qvarker/Cyclone-PCB-Factory/Hardware/CYCLONE_2/SampleGcodes/DTMF-Decoder/KicadFiles/Layout.png

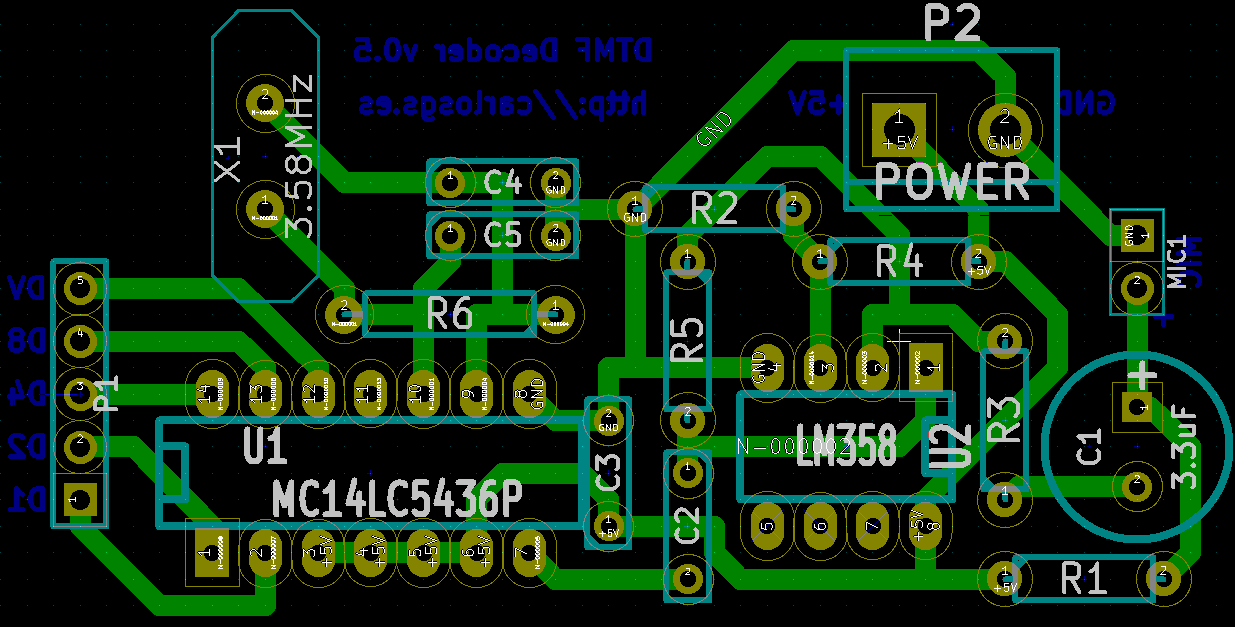
Hardware/CYCLONE_2/SampleGcodes/DTMF-Decoder/KicadFiles/Layout.png
