qvarker/Cyclone-PCB-Factory/Hardware/CYCLONE_2/SampleGcodes/DTMF-Decoder/KicadFiles/Schematic.png

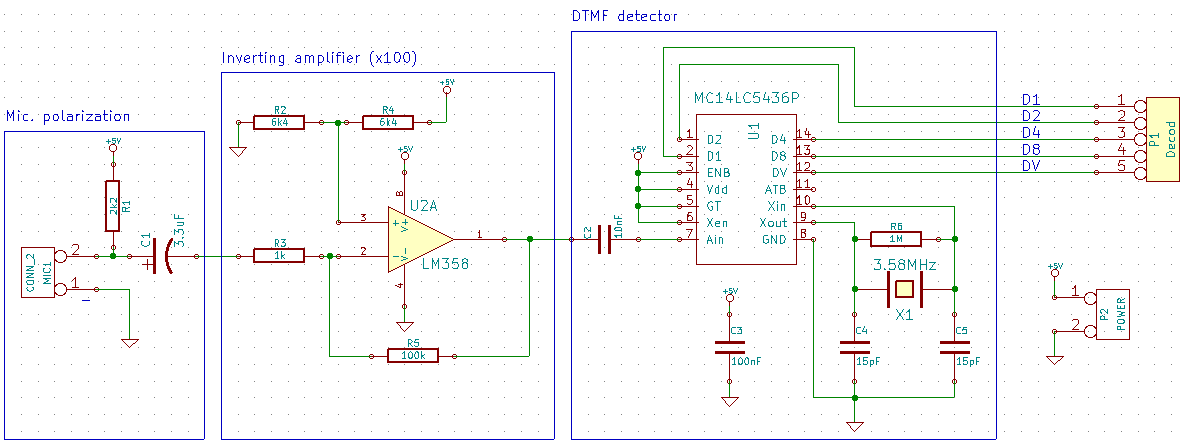
Hardware/CYCLONE_2/SampleGcodes/DTMF-Decoder/KicadFiles/Schematic.png
