qvarker/Cyclone-PCB-Factory/Hardware/CYCLONE_2/SampleGcodes/DTMF-Decoder/rapid-pcb-parameters/6.png

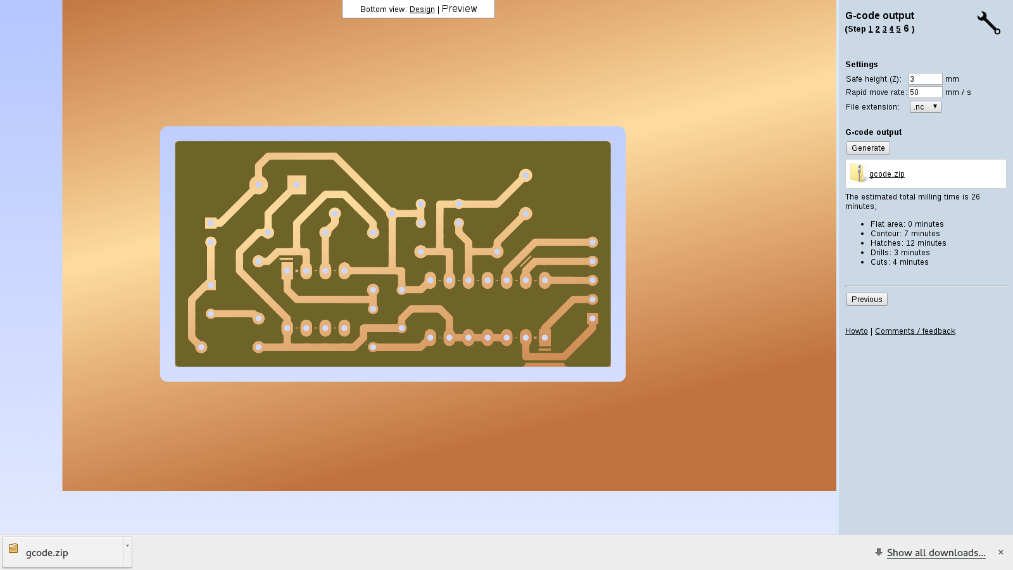
Hardware/CYCLONE_2/SampleGcodes/DTMF-Decoder/rapid-pcb-parameters/6.png
