qvarker/Cyclone-PCB-Factory/Hardware/Spindle_Pen/img/IMG_2634_display_large.jpg

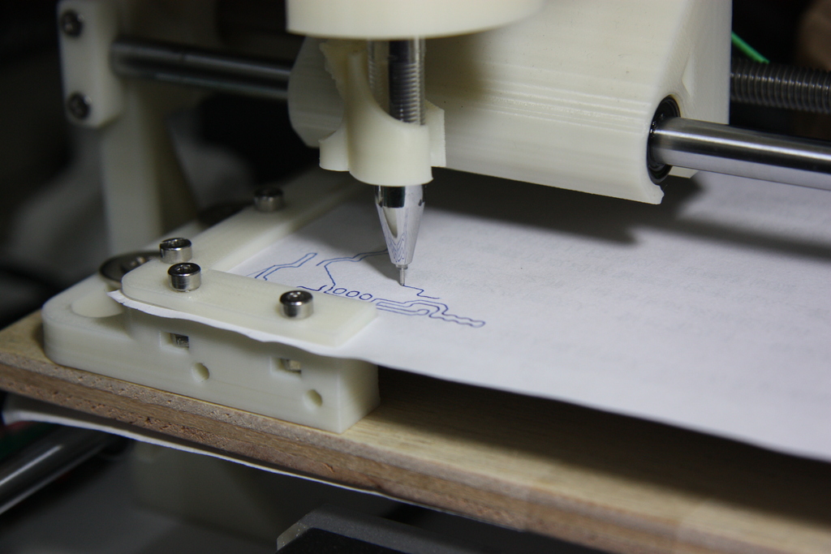
Hardware/Spindle_Pen/img/IMG_2634_display_large.jpg
