qvarker/Cyclone-PCB-Factory/Hardware/Spindle_Pen/img/IMG_9992_display_large.jpg

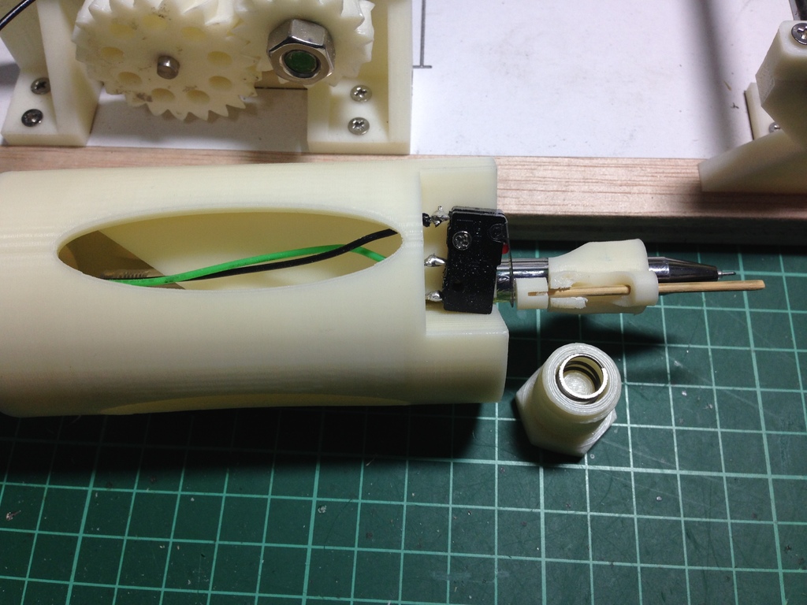
Hardware/Spindle_Pen/img/IMG_9992_display_large.jpg
