qvarker/Cyclone-PCB-Factory/Hardware/Spindle_Pen/img/SpindlePen_display_large.jpg

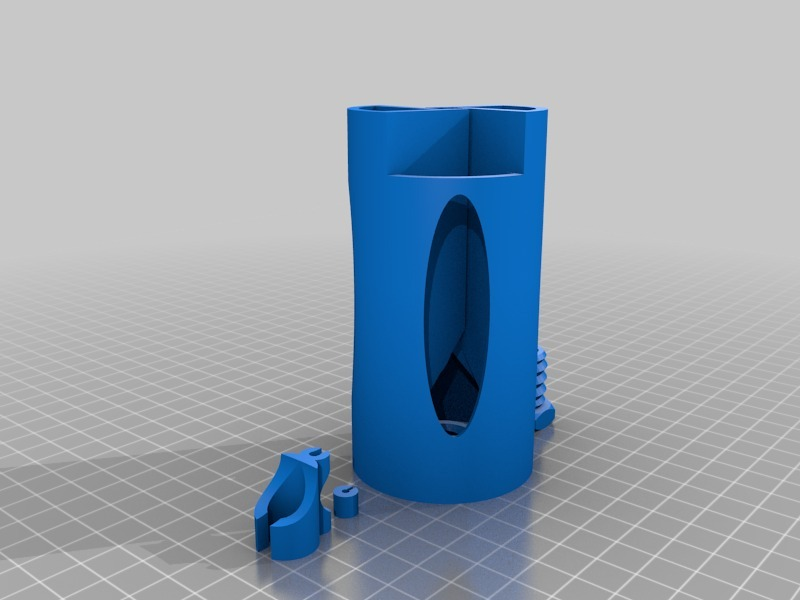
Hardware/Spindle_Pen/img/SpindlePen_display_large.jpg
