qvarker/Cyclone-PCB-Factory/Hardware/yOPERO/CNC_shieldBox/AnimationSource/frame00000.png

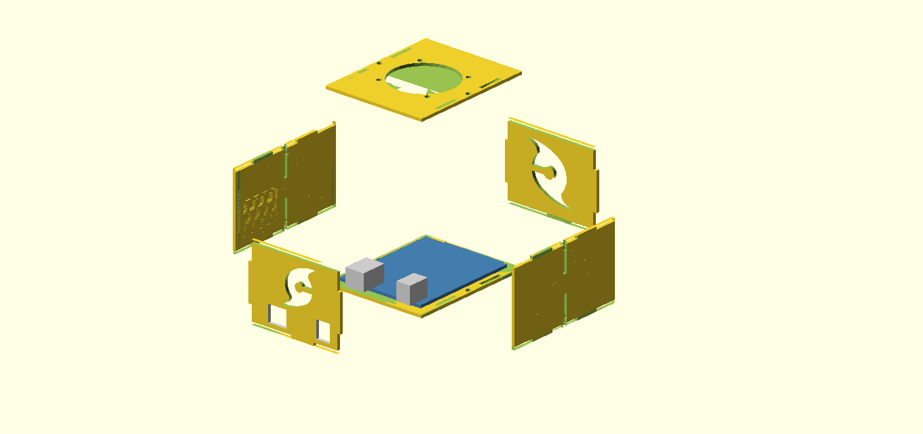
Hardware/yOPERO/CNC_shieldBox/AnimationSource/frame00000.png
