qvarker/Cyclone-PCB-Factory/Hardware/yOPERO/CNC_shieldBox/AnimationSource/frame00001.png

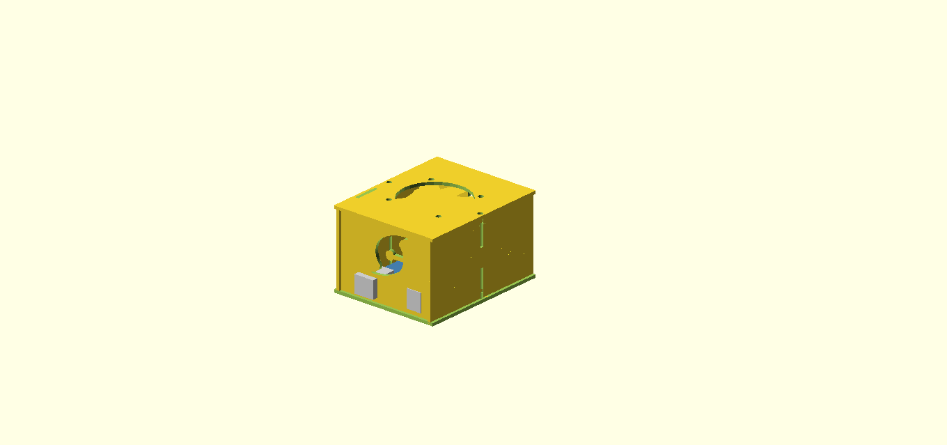
Hardware/yOPERO/CNC_shieldBox/AnimationSource/frame00001.png
