qvarker/Cyclone-PCB-Factory/Hardware/yOPERO/CNC_shieldBox/AnimationSource/frame00005.png

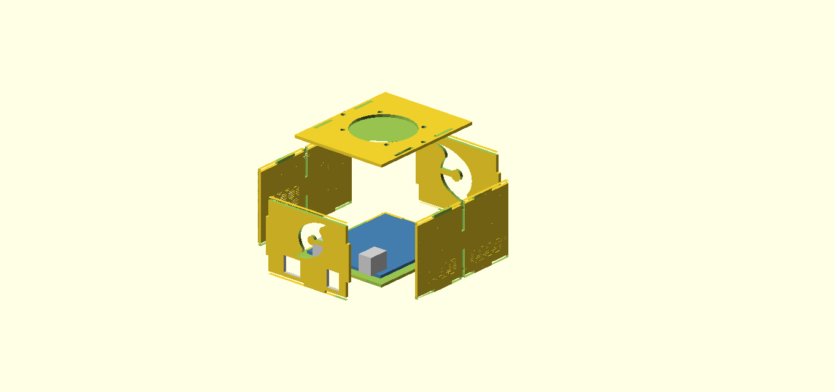
Hardware/yOPERO/CNC_shieldBox/AnimationSource/frame00005.png
