qvarker/Cyclone-PCB-Factory/Hardware/yOPERO/CNC_shieldBox/AnimationSource/frame00008.png

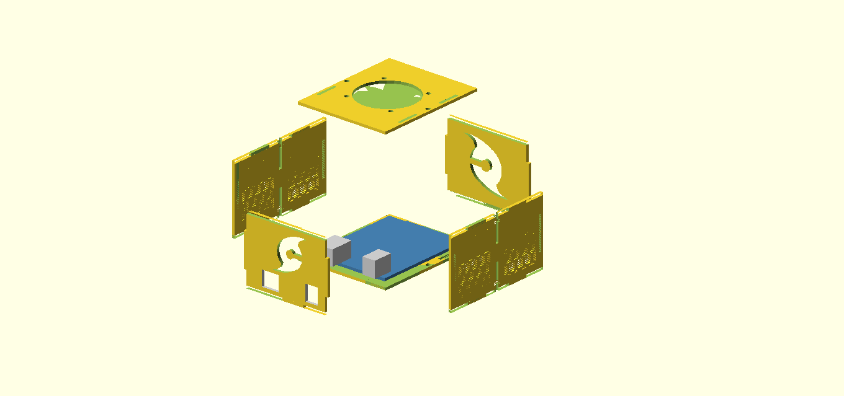
Hardware/yOPERO/CNC_shieldBox/AnimationSource/frame00008.png
