qvarker/Cyclone-PCB-Factory/Media/Cyclone_built_v0.9.5.jpg

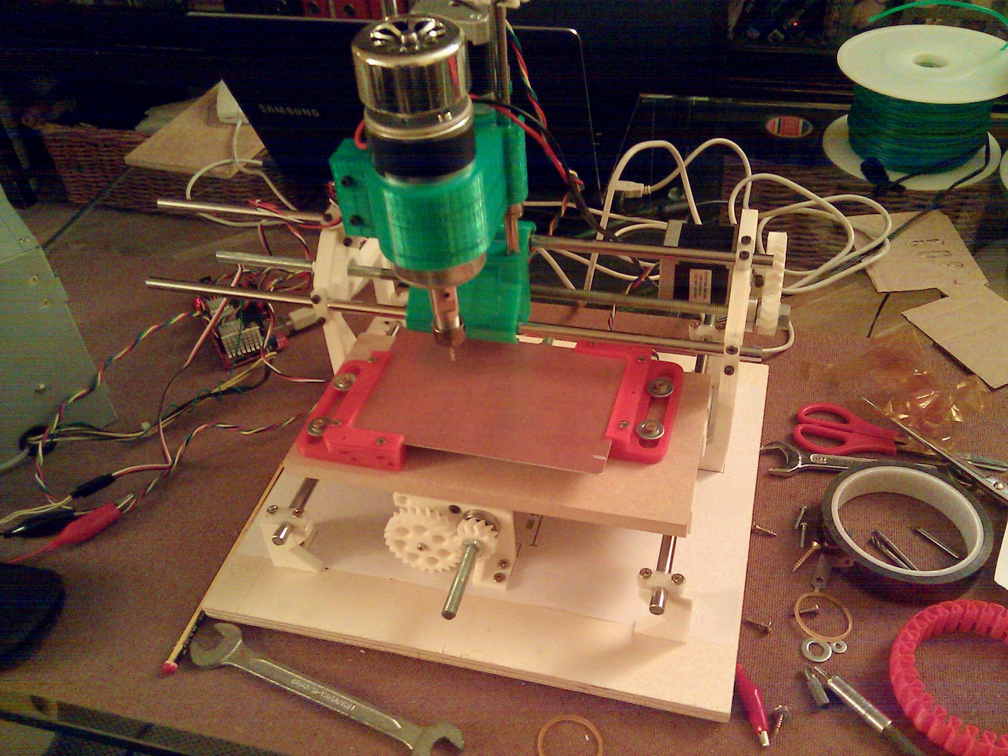
Media/Cyclone_built_v0.9.5.jpg
