qvarker/Cyclone-PCB-Factory/Media/Cyclone_render_v0.9.6.png

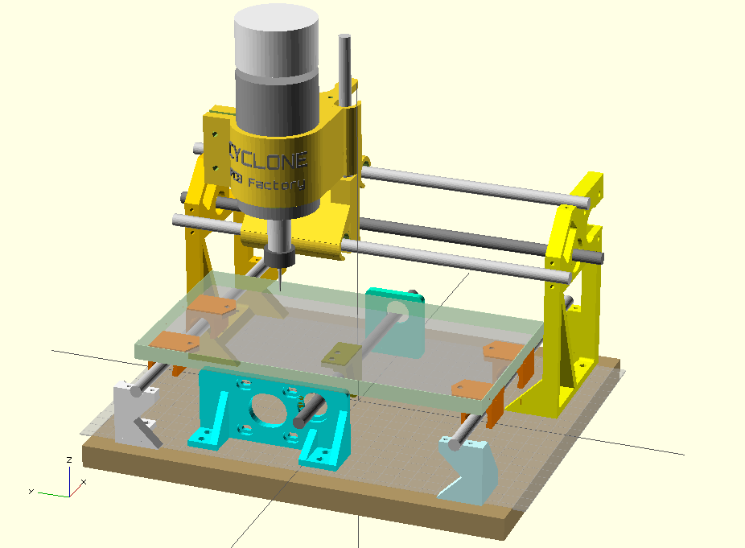
Media/Cyclone_render_v0.9.6.png
