qvarker/Cyclone-PCB-Factory/Media/Z_probing_interpolated.png

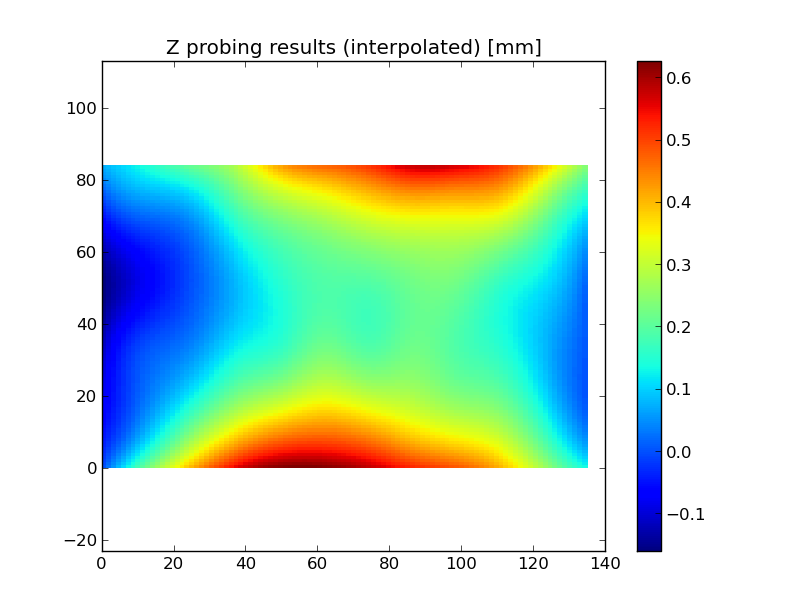
Media/Z_probing_interpolated.png
