qvarker/Cyclone-PCB-Factory/Media/Z_probing_raw.png

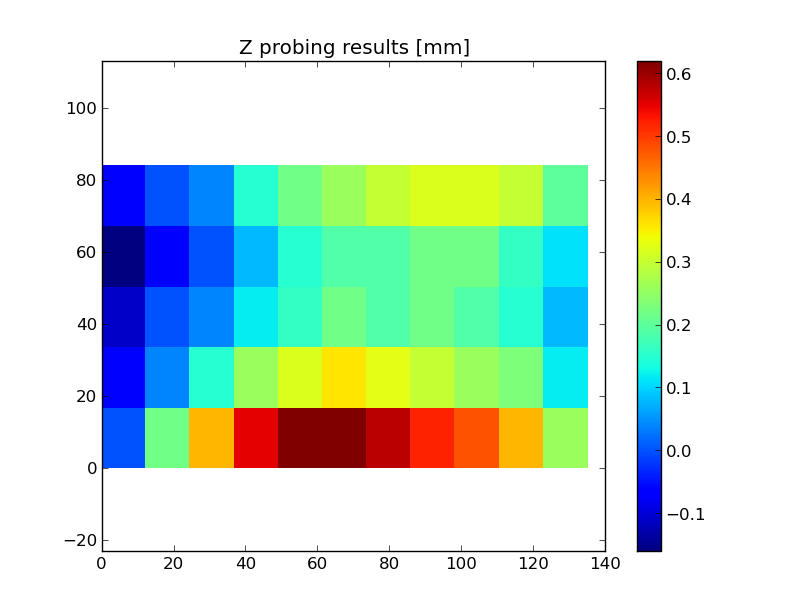
Media/Z_probing_raw.png
