qvarker/Cyclone-PCB-Factory/Software/PythonScripts/Images/DTMF.png

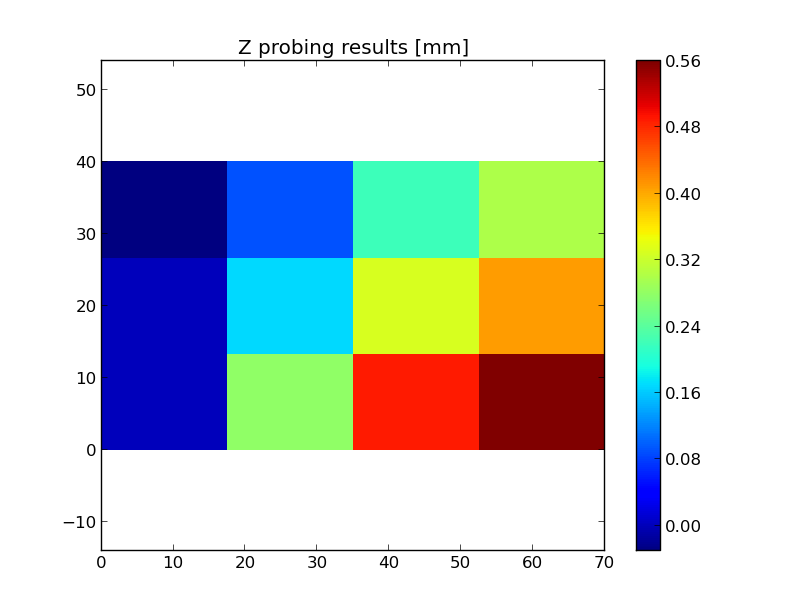
Software/PythonScripts/Images/DTMF.png
