qvarker/Cyclone-PCB-Factory/Software/PythonScripts/Images/GUI_v0.2.png

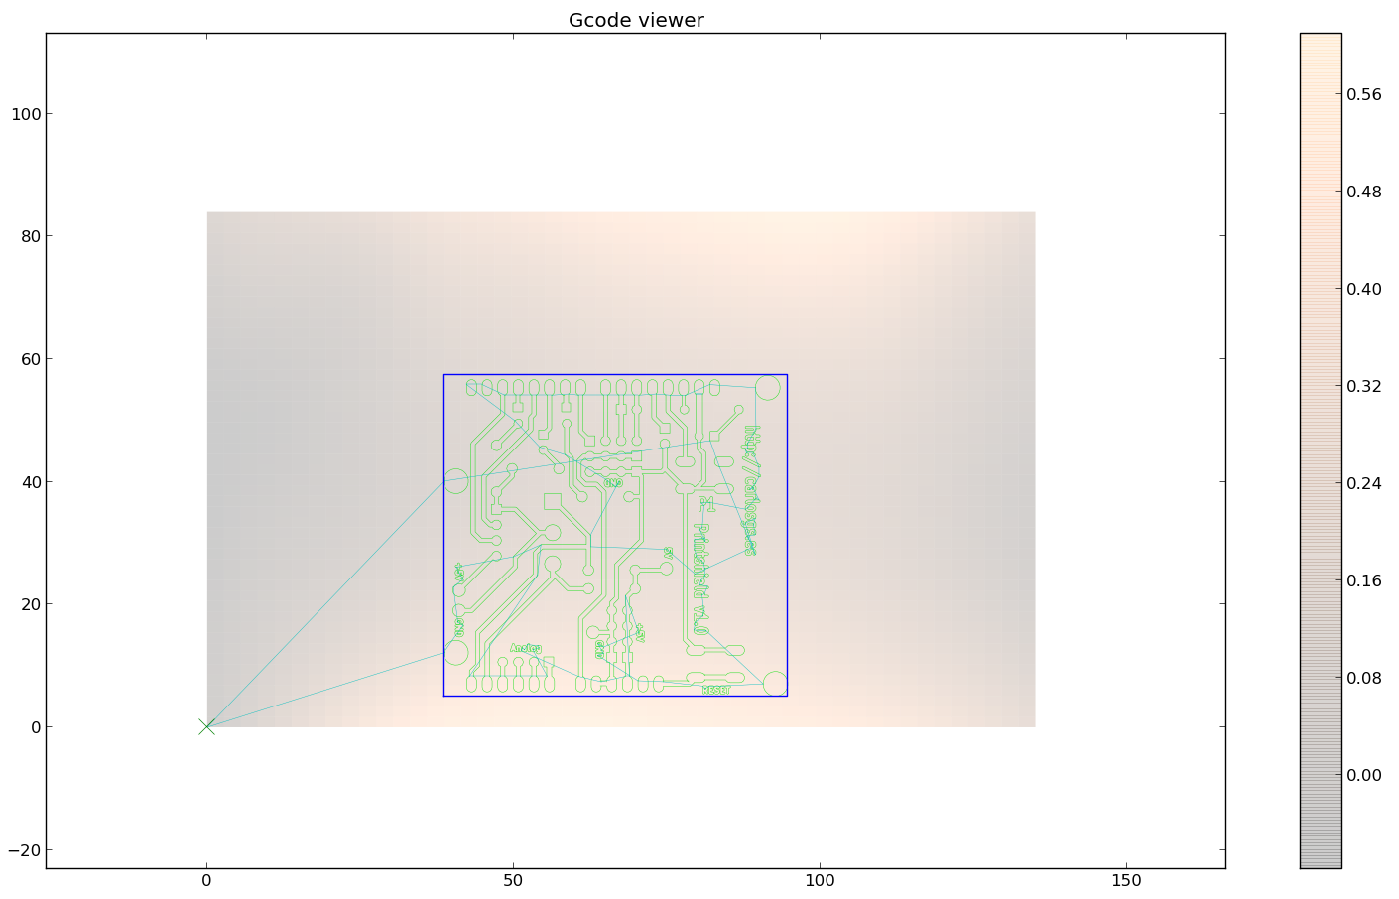
Software/PythonScripts/Images/GUI_v0.2.png
