qvarker/Cyclone-PCB-Factory/Software/PythonScripts/Images/viewGcode.png

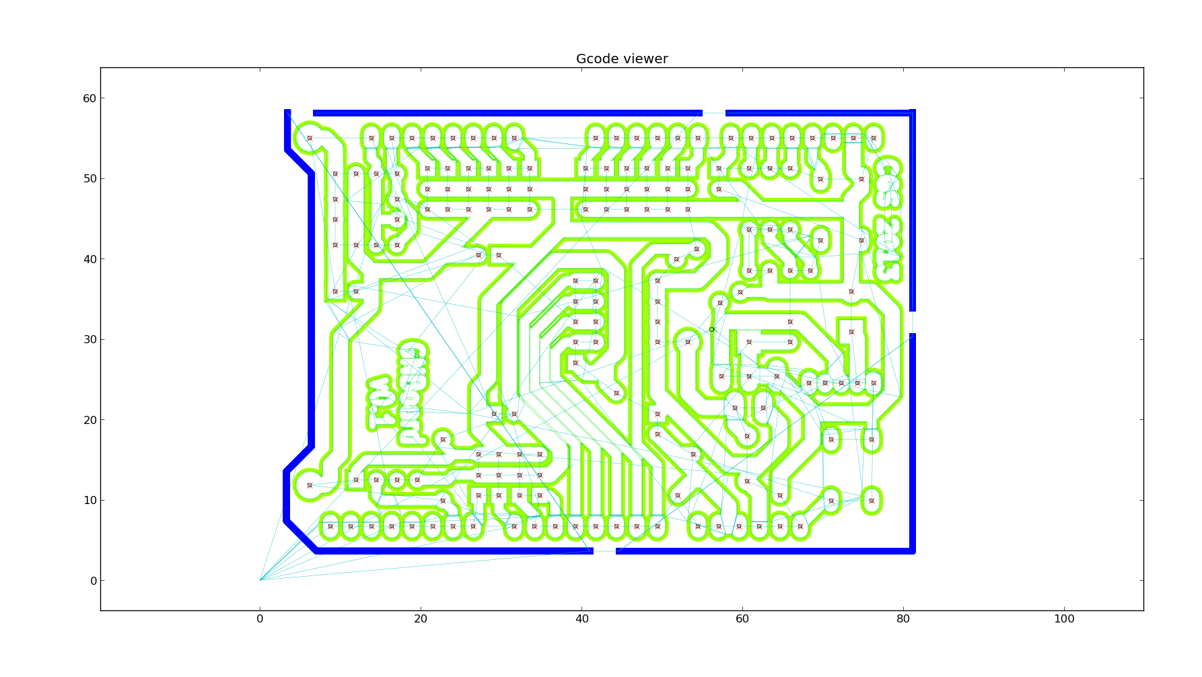
Software/PythonScripts/Images/viewGcode.png
