qvarker/Cyclone-PCB-Factory/Software/PythonScripts/Replath/replath/fullplot.bmp

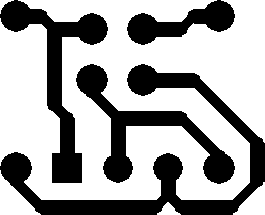
Software/PythonScripts/Replath/replath/fullplot.bmp
