qvarker/Cyclone-PCB-Factory/Hardware/smooth_rod_fix/stl/smooth_rod_fix.stl

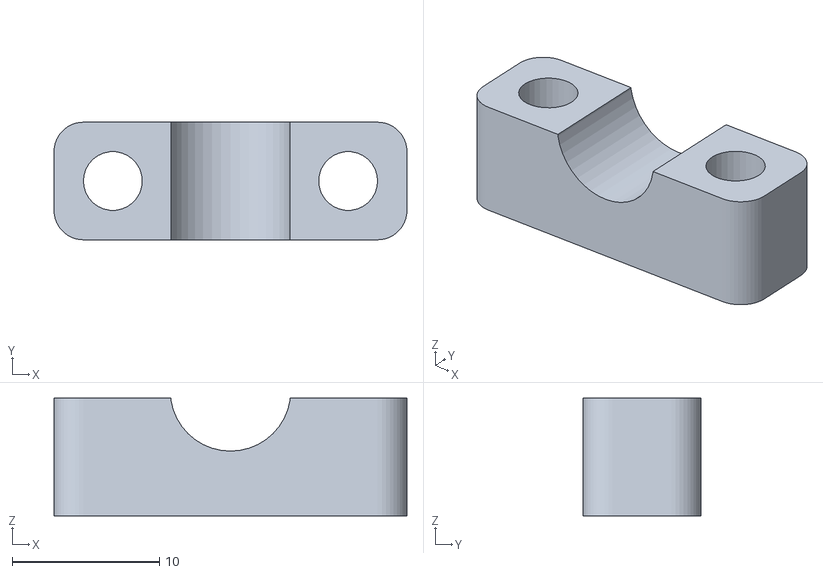
[picture p53: CAD file, 2014-09-08]
Hardware/smooth_rod_fix/stl/smooth_rod_fix.stl
24.0 x 8.00 x 8.00
