qvarker/Cyclone-PCB-Factory/Hardware/Vacuum_cleaner_attachment/prev/corrugated/vacuum_cleaner_attachment.stl

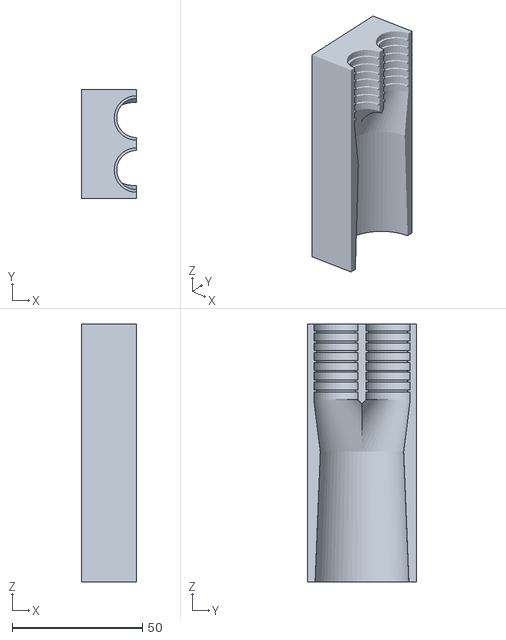
[picture p54: CAD file, 2014-09-08]
Hardware/Vacuum_cleaner_attachment/prev/corrugated/vacuum_cleaner_attachment.stl
21.0 x 42.0 x 99.0
