qvarker/Cyclone-PCB-Factory/Hardware/Vacuum_cleaner_attachment/prev/vacuum_cleaner_attachment_2_3.stl

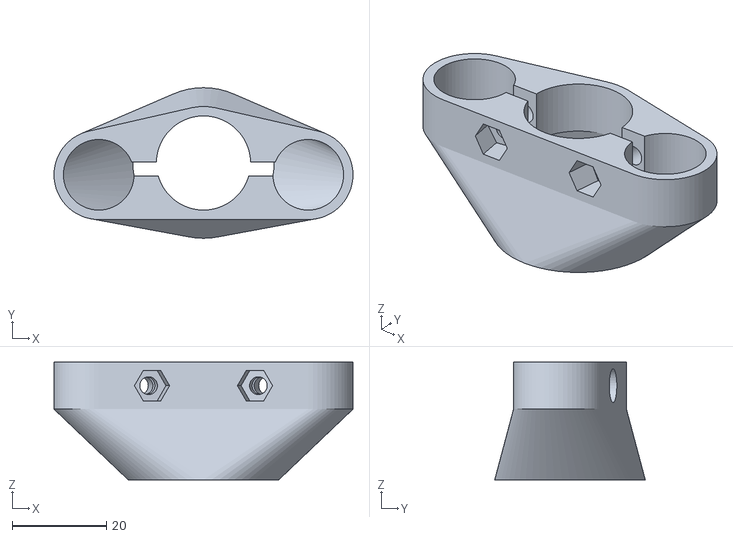
[picture p55: CAD file, 2014-09-08]
Hardware/Vacuum_cleaner_attachment/prev/vacuum_cleaner_attachment_2_3.stl
63.5 x 32.0 x 25.0
