qvarker/Cyclone-PCB-Factory/Hardware/Vacuum_cleaner_attachment/vacuum_cleaner_attachment.stl

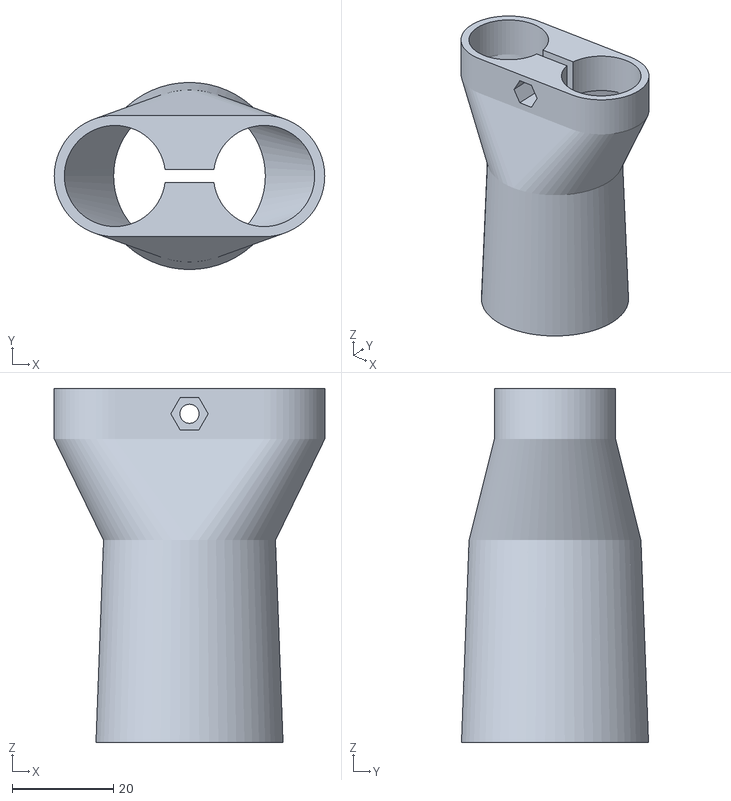
[picture p56: CAD file, 2014-09-08]
Hardware/Vacuum_cleaner_attachment/vacuum_cleaner_attachment.stl
53.5 x 37.0 x 70.0
