qvarker/Cyclone-PCB-Factory/Hardware/XZ_axis/stl/gears/motor_gear.stl

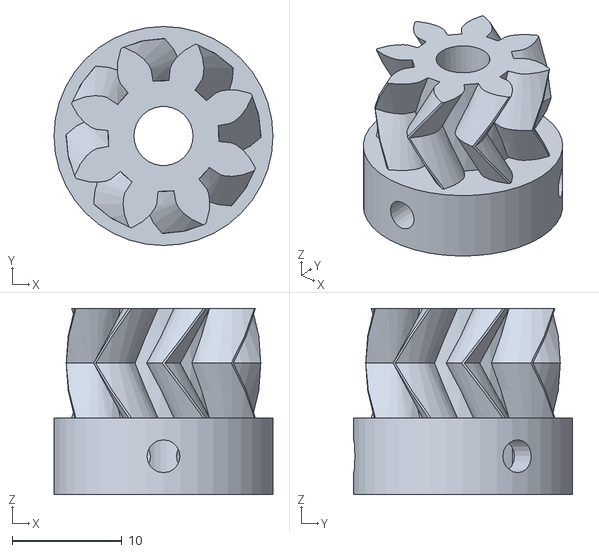
[picture p57: CAD file, 2014-09-08]
Hardware/XZ_axis/stl/gears/motor_gear.stl
20.0 x 20.0 x 17.0
