qvarker/Cyclone-PCB-Factory/Hardware/XZ_axis/stl/Z_carriage_bottom.stl

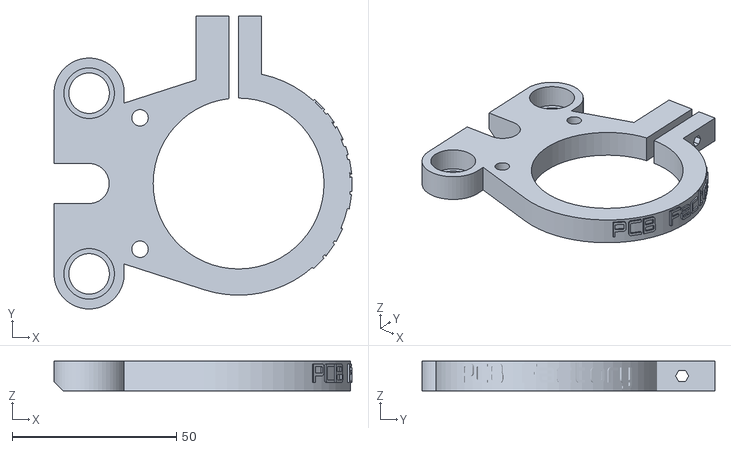
[picture p58: CAD file, 2014-09-08]
Hardware/XZ_axis/stl/Z_carriage_bottom.stl
90.7 x 89.2 x 9.00
