qvarker/Cyclone-PCB-Factory/Hardware/Y_axis/stl/motor_stand.stl

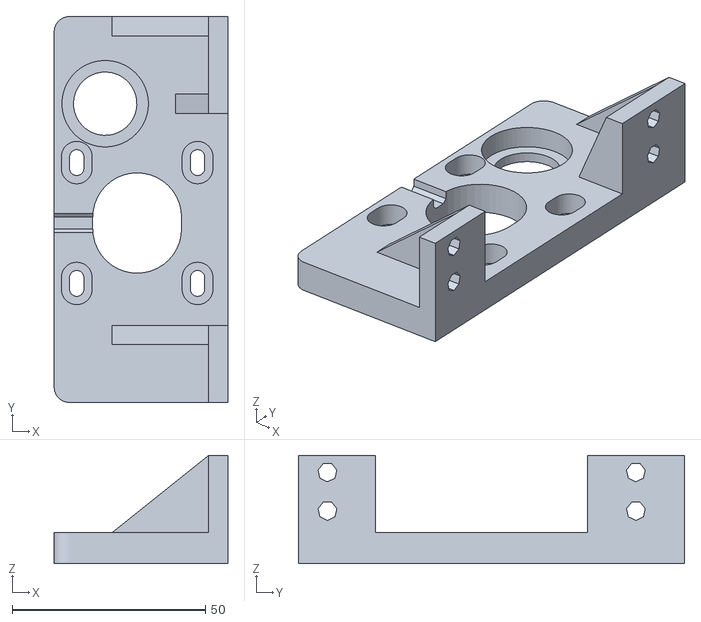
[picture p59: CAD file, 2014-09-08]
Hardware/Y_axis/stl/motor_stand.stl
45.0 x 100.0 x 28.0
