qvarker/Cyclone-PCB-Factory/Hardware/Y_axis/stl/Y_rod_idlers/Y_rod_idler_right.stl

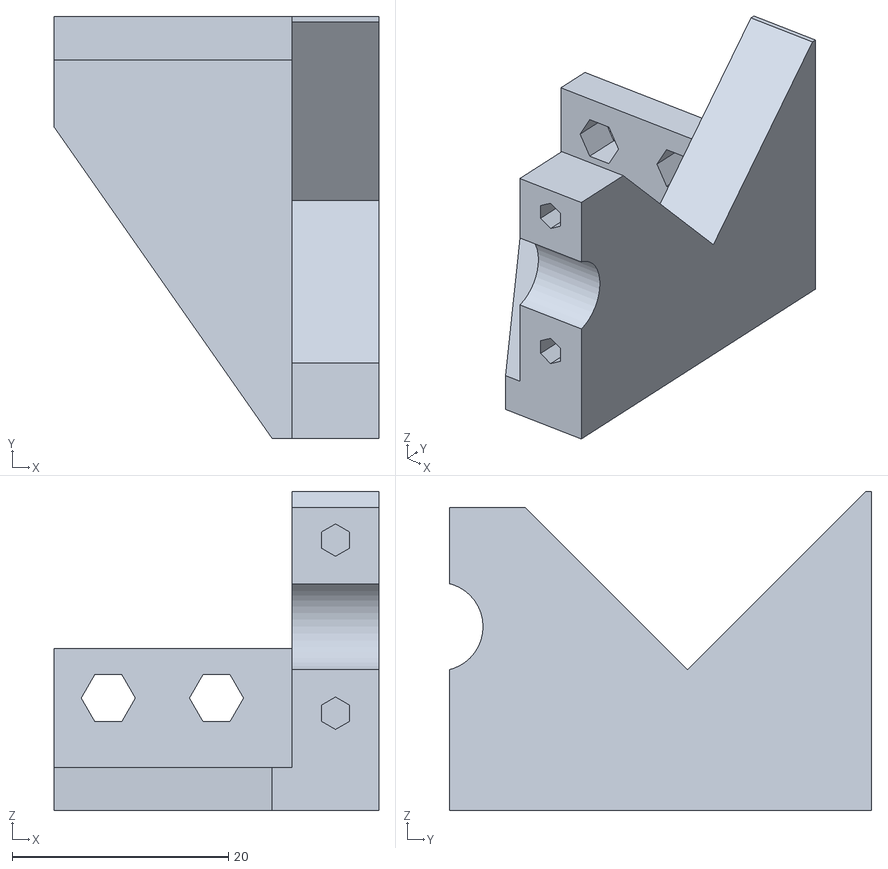
[picture p60: CAD file, 2014-09-08]
Hardware/Y_axis/stl/Y_rod_idlers/Y_rod_idler_right.stl
30.0 x 39.0 x 29.5
