qvarker/Cyclone-PCB-Factory/Hardware/yOPERO/CNC_shieldBox/STL/back.stl

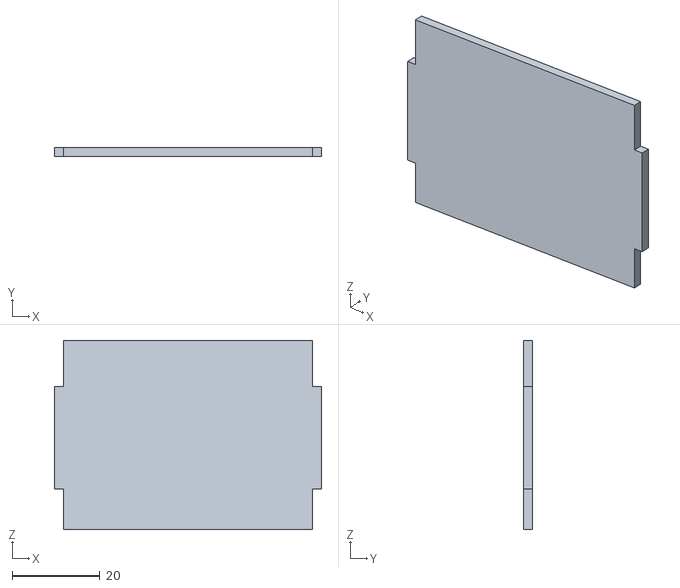
[picture p61: CAD file, 2014-09-08]
Hardware/yOPERO/CNC_shieldBox/STL/back.stl
60.7 x 2.00 x 43.0
