qvarker/Cyclone-PCB-Factory/Hardware/yOPERO/CNC_shieldBox/STL/Template/cncElectronicsShield.stl

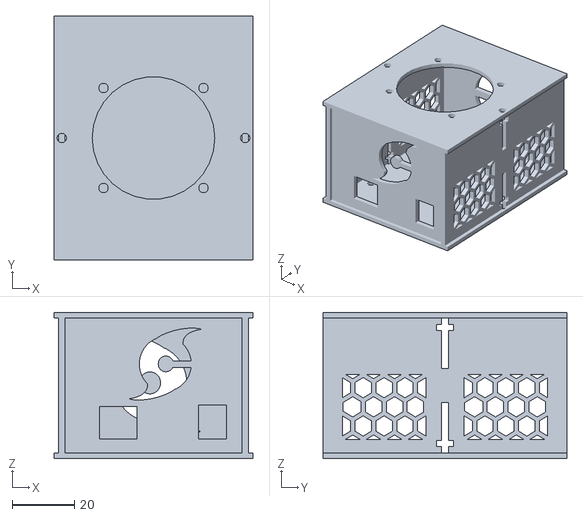
[picture p62: CAD file, 2014-09-08]
Hardware/yOPERO/CNC_shieldBox/STL/Template/cncElectronicsShield.stl
63.7 x 78.0 x 46.8
