qvarker/Cyclone-PCB-Factory/Hardware/yOPERO/Cyclone_Template/output/template_workbed.dxf

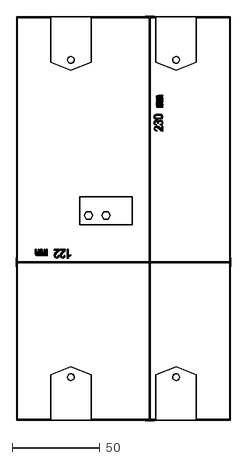
[picture p63: CAD file, 2014-09-08]
Hardware/yOPERO/Cyclone_Template/output/template_workbed.dxf
122.5 x 230.5
