qvarker/Cyclone-PCB-Factory/Hardware/yOPERO/Gears/stl/rod_gear.stl

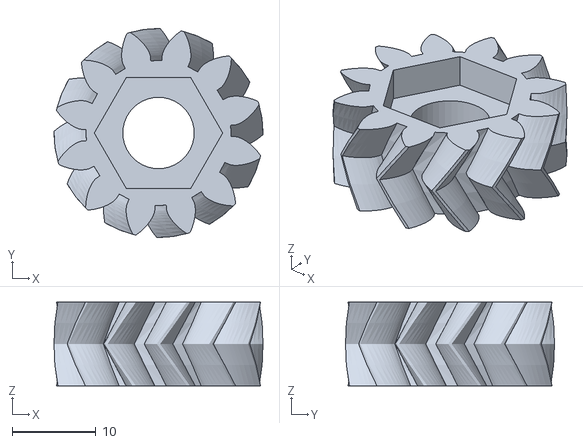
[picture p64: CAD file, 2014-09-08]
Hardware/yOPERO/Gears/stl/rod_gear.stl
24.9 x 24.9 x 10.0
