qvarker/Cyclone-PCB-Factory/Hardware/yOPERO/main_frame/stl/frame_hex_back support.stl

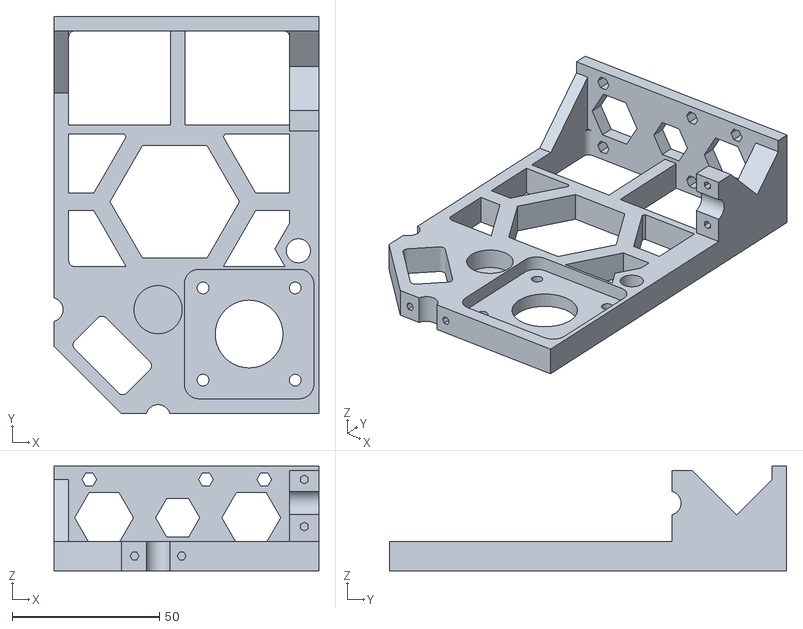
[picture p65: CAD file, 2014-09-08]
Hardware/yOPERO/main_frame/stl/frame_hex_back support.stl
90.0 x 135.0 x 35.5
