qvarker/Cyclone-PCB-Factory/Hardware/yOPERO/main_frame/stl/not used/frame.stl

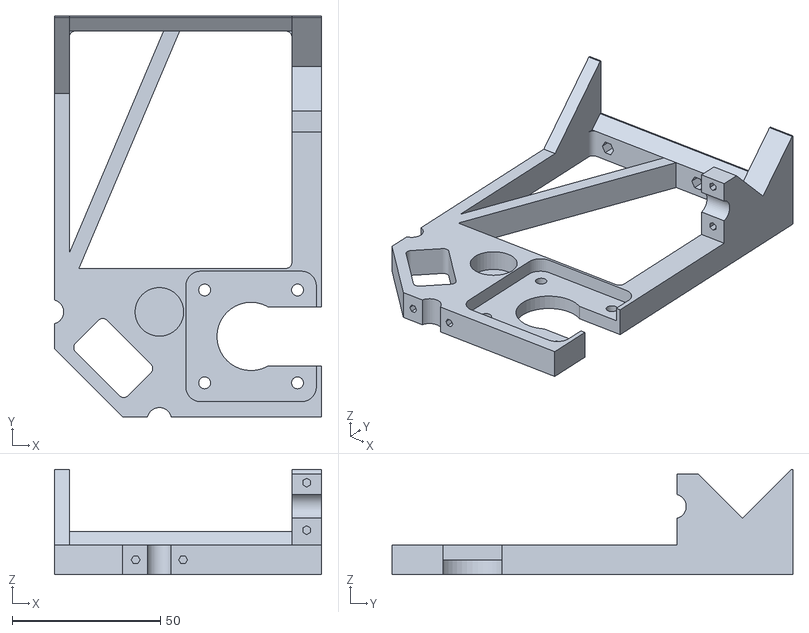
[picture p66: CAD file, 2014-09-08]
Hardware/yOPERO/main_frame/stl/not used/frame.stl
90.0 x 135.0 x 35.5
