qvarker/Cyclone-PCB-Factory/Hardware/yOPERO/smooth_rod_fix/stl/smooth_rod_fix_x8.stl

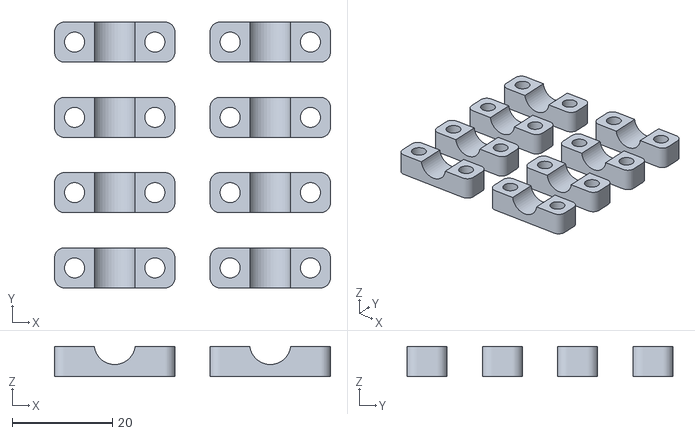
[picture p67: CAD file, 2014-09-08]
Hardware/yOPERO/smooth_rod_fix/stl/smooth_rod_fix_x8.stl
55.0 x 53.0 x 6.00
