qvarker/Cyclone-PCB-Factory/Hardware/yOPERO/XZ_axis/stl/X_carriage_YOP.stl

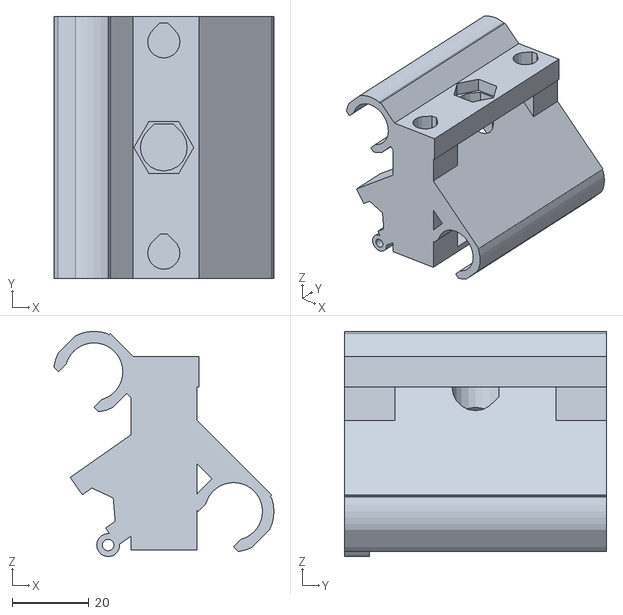
[picture p68: CAD file, 2014-09-08]
Hardware/yOPERO/XZ_axis/stl/X_carriage_YOP.stl
57.3 x 68.2 x 58.6
