qvarker/Cyclone-PCB-Factory/Hardware/yOPERO/Y_axis/cyclone_logo1.dxf

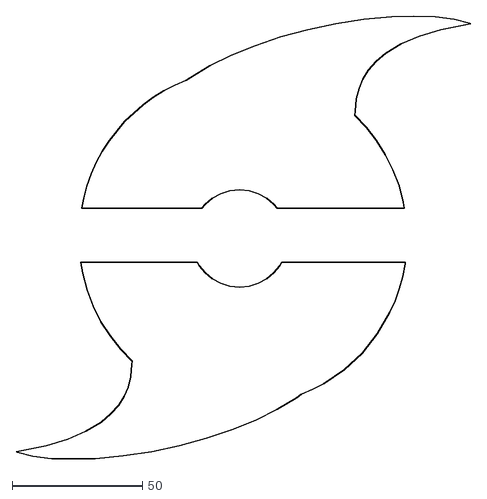
[picture p69: CAD file, 2014-09-08]
Hardware/yOPERO/Y_axis/cyclone_logo1.dxf
174.3 x 169.6
