qvarker/Cyclone-PCB-Factory/Hardware/yOPERO/Y_axis/stl/motor_holder.stl

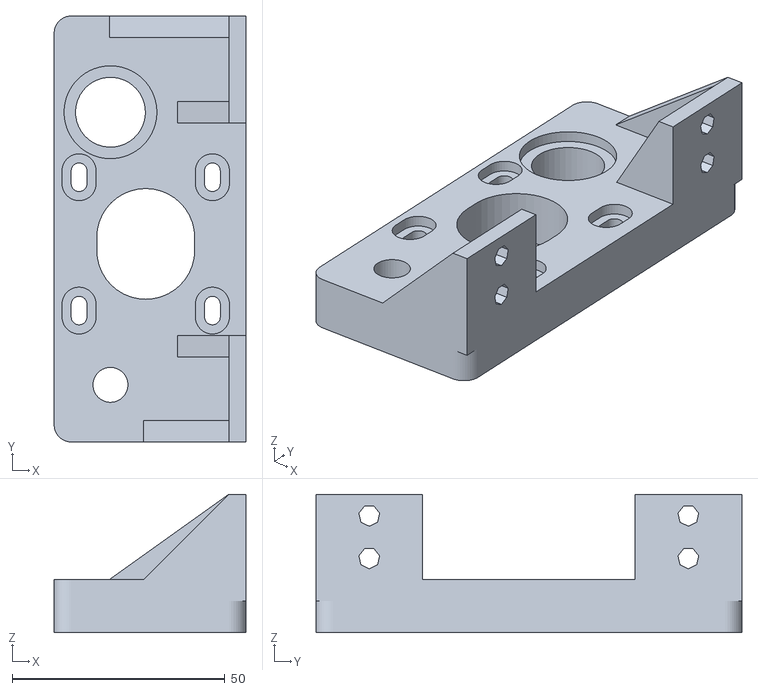
[picture p70: CAD file, 2014-09-08]
Hardware/yOPERO/Y_axis/stl/motor_holder.stl
45.0 x 100.0 x 32.5
