qvarker/Cyclone-PCB-Factory/Media/CycloneLogo_1/CycloneLogo_1.dxf

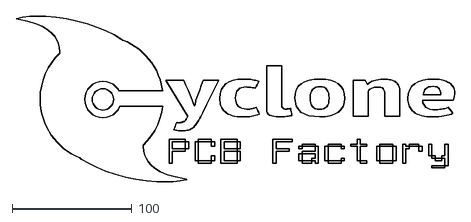
[picture p71: CAD file, 2014-09-08]
Media/CycloneLogo_1/CycloneLogo_1.dxf
366.4 x 138.5
