qvarker/Cyclone-PCB-Factory/Hardware/CYCLONE_2/dxf/oshw.dxf

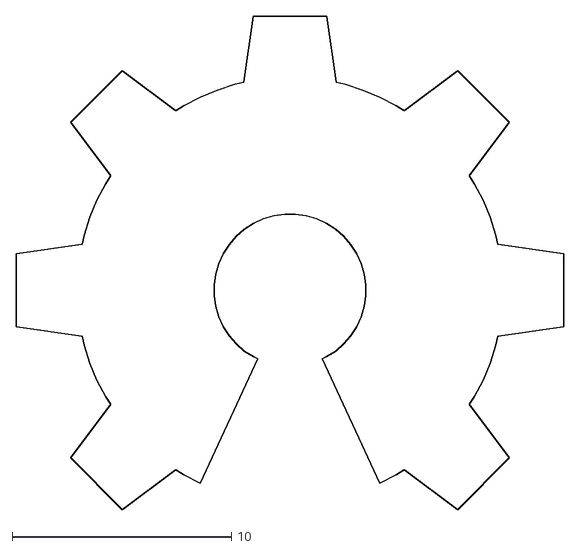
[picture p72: CAD file, 2014-08-22]
Hardware/CYCLONE_2/dxf/oshw.dxf
25.0 x 22.5
