qvarker/Cyclone-PCB-Factory/Hardware/CYCLONE_2/freecad/Cyclone_X_rightFrame.fcstd

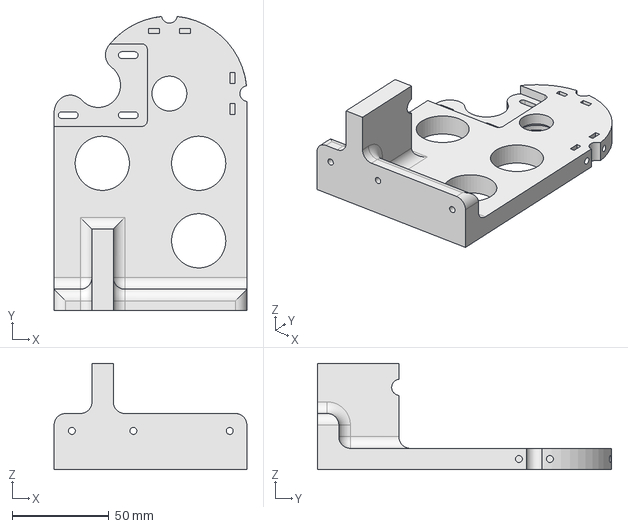
[picture p73: CAD file, 2014-09-10]
Hardware/CYCLONE_2/freecad/Cyclone_X_rightFrame.fcstd
99.5 x 151.8 x 54.9 mm
