qvarker/Cyclone-PCB-Factory/Hardware/CYCLONE_2/INHERITED/stl/vacuum_cleaner_attachment_2.stl

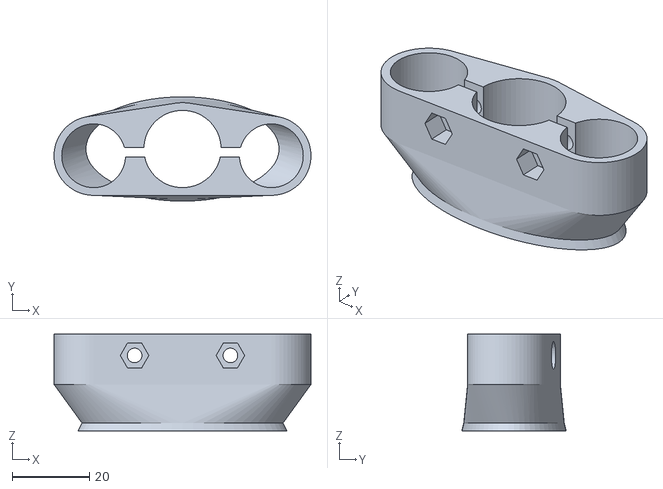
[picture p74: CAD file, 2014-09-08]
Hardware/CYCLONE_2/INHERITED/stl/vacuum_cleaner_attachment_2.stl
66.5 x 27.0 x 25.0
