qvarker/Cyclone-PCB-Factory/Hardware/CYCLONE_2/INHERITED/XYgears/XYmotor_gear.stl

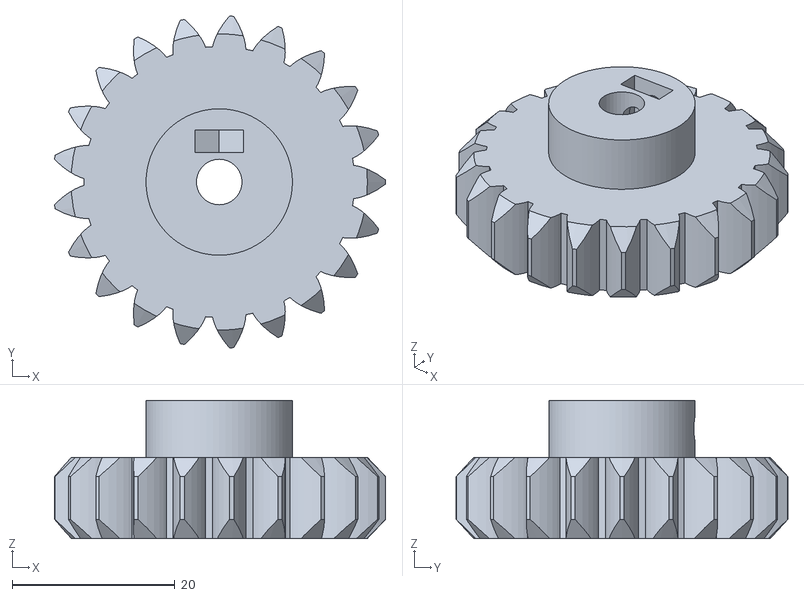
[picture p75: CAD file, 2014-08-22]
Hardware/CYCLONE_2/INHERITED/XYgears/XYmotor_gear.stl
40.7 x 40.8 x 17.0
