qvarker/Cyclone-PCB-Factory/Hardware/CYCLONE_2/INHERITED/Zgears/Zmotor_gear.stl

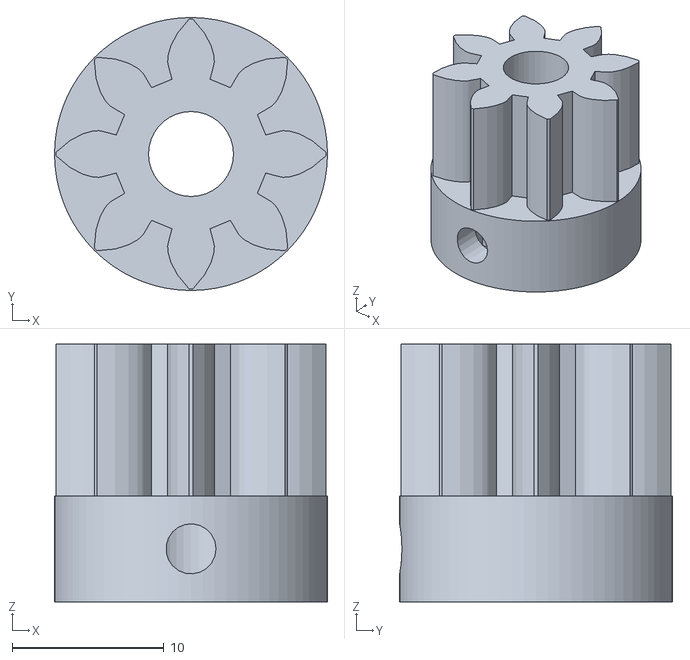
[picture p76: CAD file, 2014-08-22]
Hardware/CYCLONE_2/INHERITED/Zgears/Zmotor_gear.stl
18.0 x 18.0 x 17.0
