qvarker/Cyclone-PCB-Factory/Hardware/CYCLONE_2/output/ShorterVersion/Cyclone_XleftFrame.stl

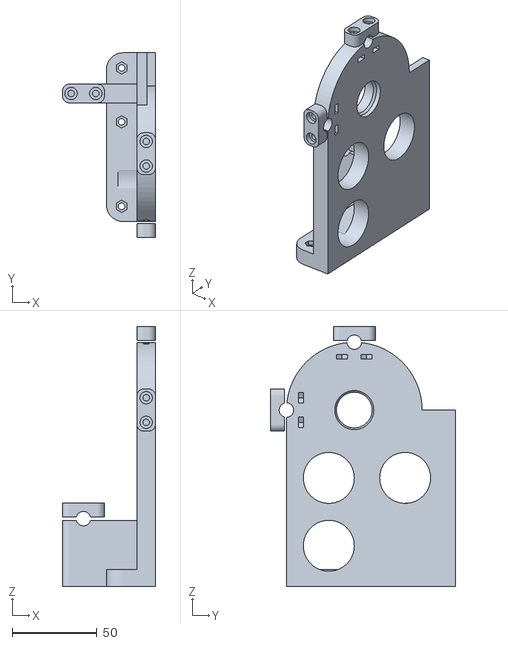
[picture p77: CAD file, 2014-09-08]
Hardware/CYCLONE_2/output/ShorterVersion/Cyclone_XleftFrame.stl
54.9 x 108.8 x 153.2
