qvarker/Cyclone-PCB-Factory/Hardware/CYCLONE_2/output/templates/Cyclone_workbed_template.dxf

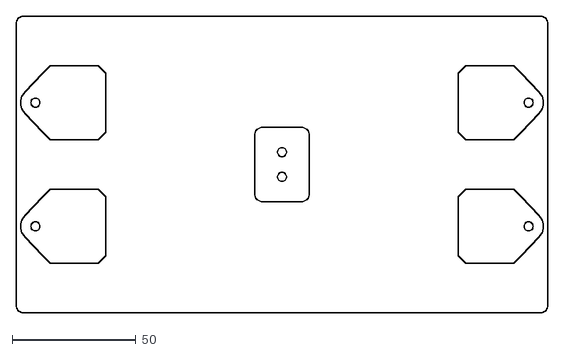
[picture p78: CAD file, 2014-08-22]
Hardware/CYCLONE_2/output/templates/Cyclone_workbed_template.dxf
215.0 x 120.0
