qvarker/Cyclone-PCB-Factory/Hardware/CYCLONE_2/output/templates/laserCut/Cyclone_workbed_8mm.dxf

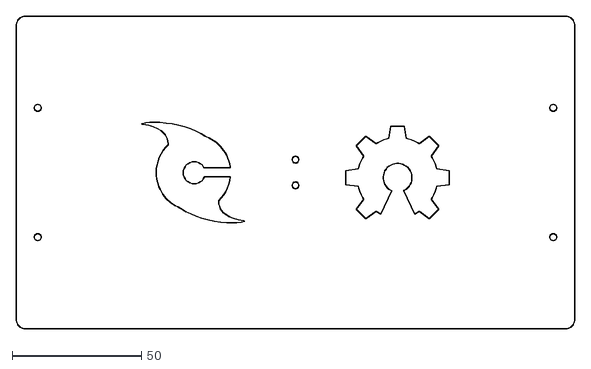
[picture p79: CAD file, 2014-08-22]
Hardware/CYCLONE_2/output/templates/laserCut/Cyclone_workbed_8mm.dxf
216.0 x 121.0
