qvarker/Cyclone-PCB-Factory/Hardware/CYCLONE_2/output/templates/laserCut/separate/Cyclone_base_drills.dxf

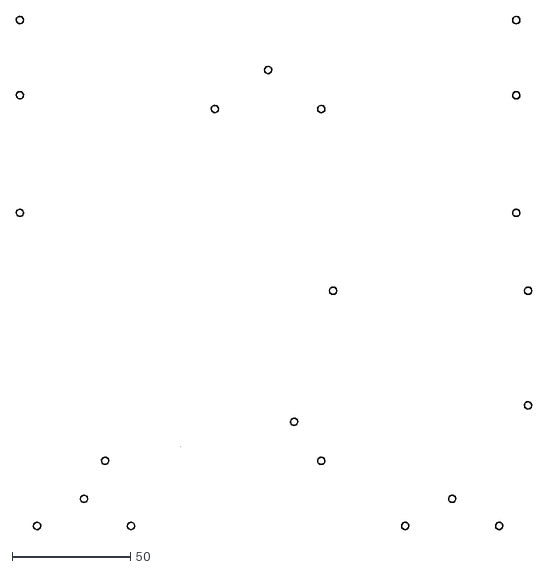
[picture p80: CAD file, 2014-08-22]
Hardware/CYCLONE_2/output/templates/laserCut/separate/Cyclone_base_drills.dxf
218.1 x 217.1
