qvarker/Cyclone-PCB-Factory/Hardware/Gears/stl/motor_gear_21.stl

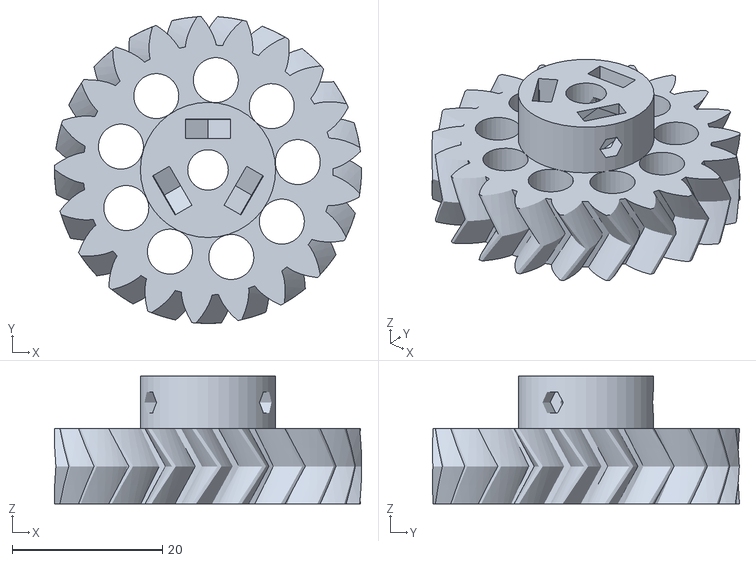
[picture p81: CAD file, 2014-09-08]
Hardware/Gears/stl/motor_gear_21.stl
40.9 x 40.9 x 17.0
