qvarker/Cyclone-PCB-Factory/Hardware/main_frame/Flat_DXFs/frame_nomotor.dxf

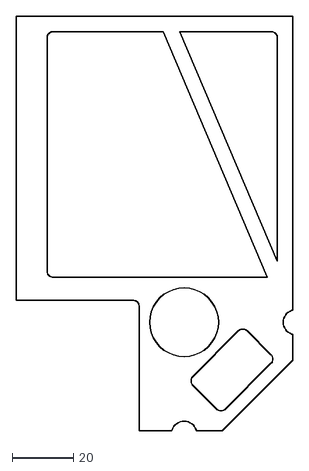
[picture p82: CAD file, 2014-09-08]
Hardware/main_frame/Flat_DXFs/frame_nomotor.dxf
90.0 x 135.0
