qvarker/Cyclone-PCB-Factory/Hardware/main_frame/stl/frame.stl

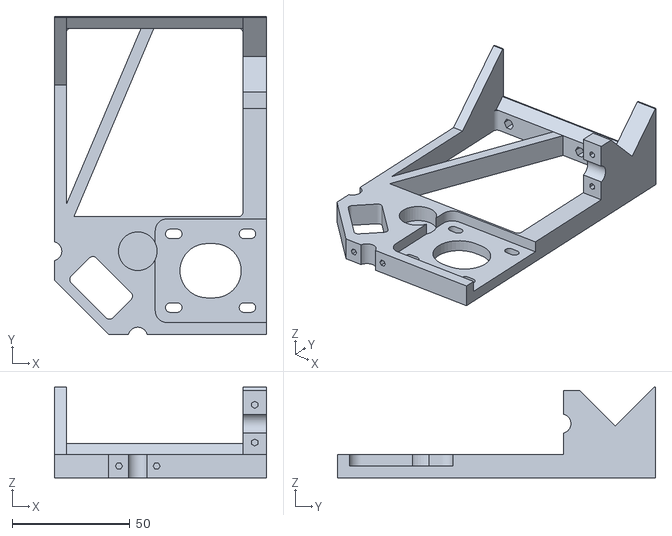
[picture p83: CAD file, 2014-09-08]
Hardware/main_frame/stl/frame.stl
90.0 x 135.0 x 38.5
