qvarker/Cyclone-PCB-Factory/Hardware/smooth_rod_fix/stl/smooth_rod_fix_x4.stl

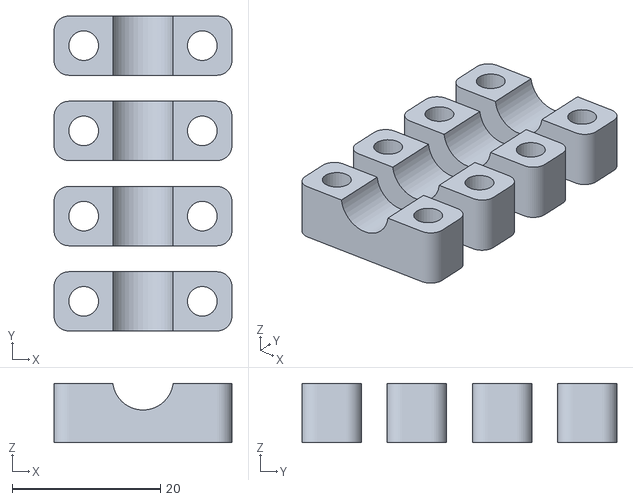
[picture p84: CAD file, 2014-09-08]
Hardware/smooth_rod_fix/stl/smooth_rod_fix_x4.stl
24.0 x 42.5 x 8.00
