qvarker/Cyclone-PCB-Factory/Hardware/Vacuum_cleaner_attachment/prev/corrugated/vacuum_cleaner_attachment_2.stl

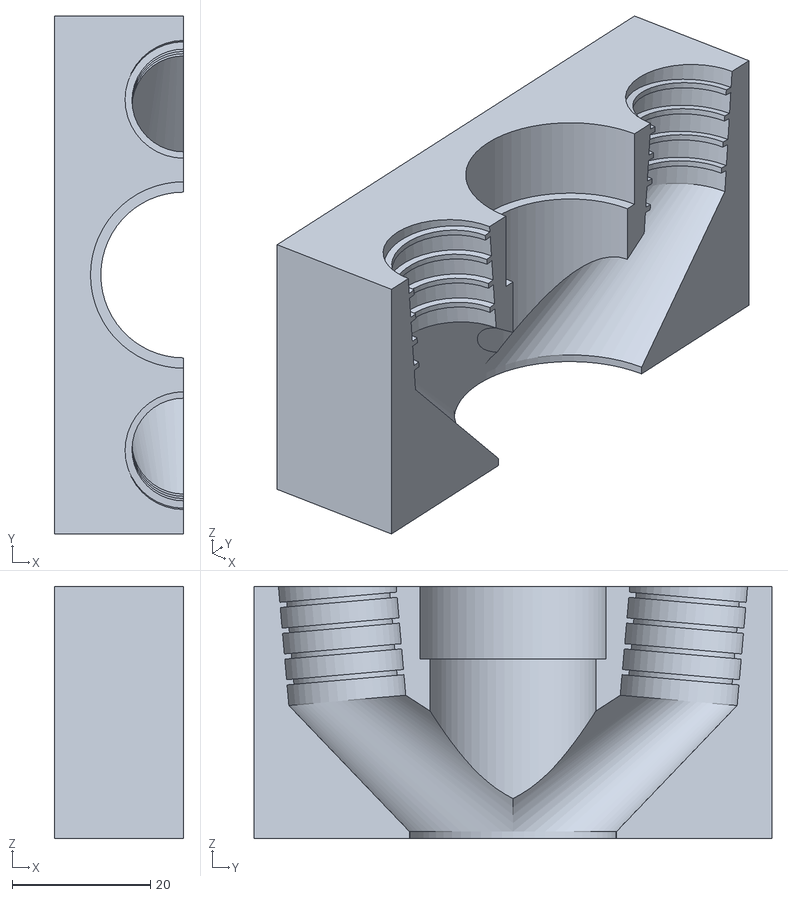
[picture p85: CAD file, 2014-09-08]
Hardware/Vacuum_cleaner_attachment/prev/corrugated/vacuum_cleaner_attachment_2.stl
18.8 x 75.0 x 36.5
