qvarker/Cyclone-PCB-Factory/Hardware/Vacuum_cleaner_attachment/prev/vacuum_cleaner_attachment_2_2.stl

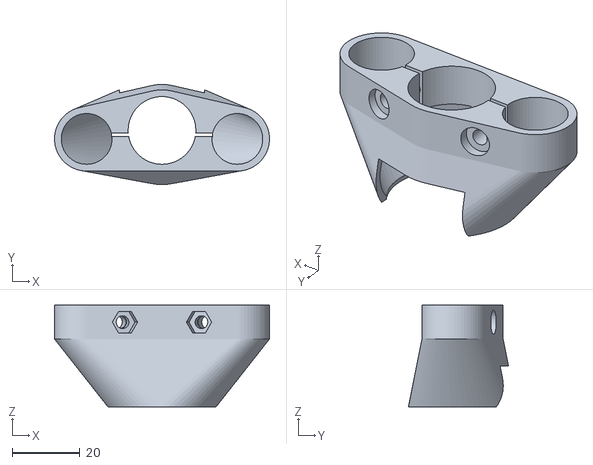
[picture p86: CAD file, 2014-09-08]
Hardware/Vacuum_cleaner_attachment/prev/vacuum_cleaner_attachment_2_2.stl
63.5 x 29.6 x 30.0
