qvarker/Cyclone-PCB-Factory/Hardware/Vacuum_cleaner_attachment/vacuum_cleaner_attachment_2.stl

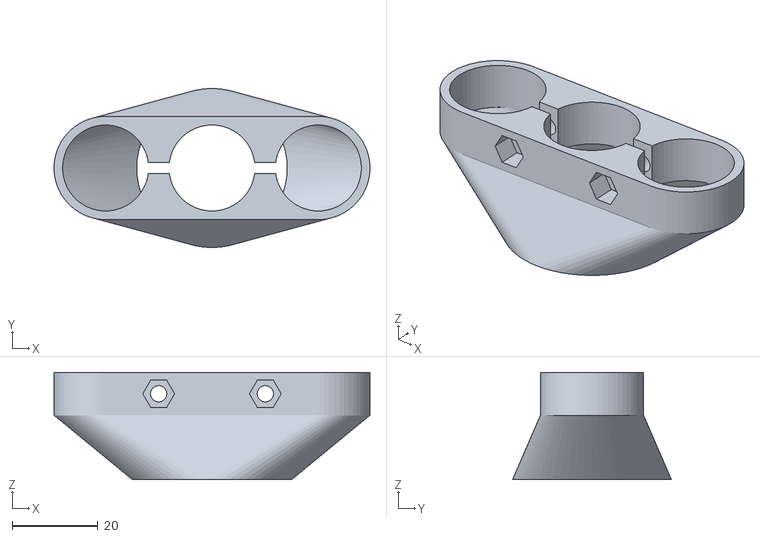
[picture p87: CAD file, 2014-08-22]
Hardware/Vacuum_cleaner_attachment/vacuum_cleaner_attachment_2.stl
73.5 x 37.0 x 25.0
