qvarker/Cyclone-PCB-Factory/Hardware/XZ_axis/stl/gears/rod_gear.stl

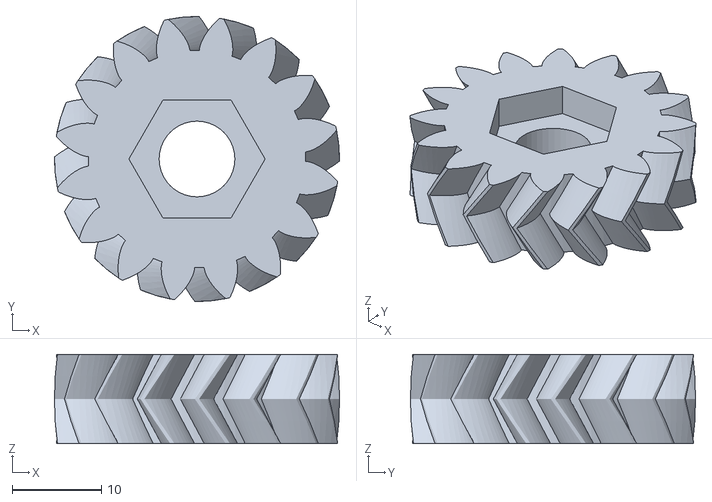
[picture p88: CAD file, 2014-09-08]
Hardware/XZ_axis/stl/gears/rod_gear.stl
32.0 x 32.0 x 10.0
