qvarker/Cyclone-PCB-Factory/Hardware/XZ_axis/stl/X_carriage.stl

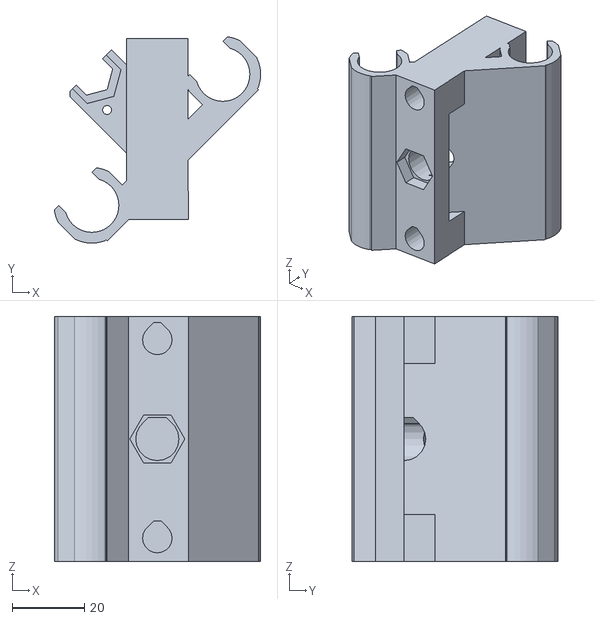
[picture p89: CAD file, 2014-09-08]
Hardware/XZ_axis/stl/X_carriage.stl
57.3 x 57.3 x 68.0
