qvarker/Cyclone-PCB-Factory/Hardware/Y_axis/stl/idle_stand.stl

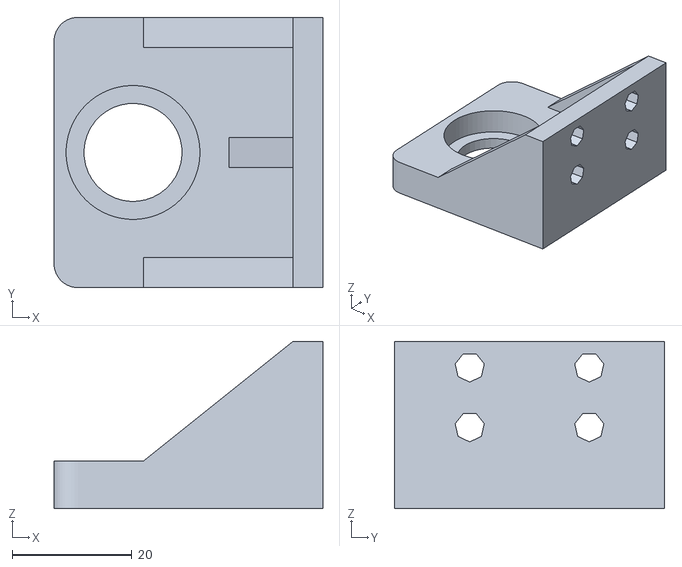
[picture p90: CAD file, 2014-09-08]
Hardware/Y_axis/stl/idle_stand.stl
45.0 x 45.2 x 28.0
