qvarker/Cyclone-PCB-Factory/Hardware/yOPERO/CNC_shieldBox/STL/top.stl

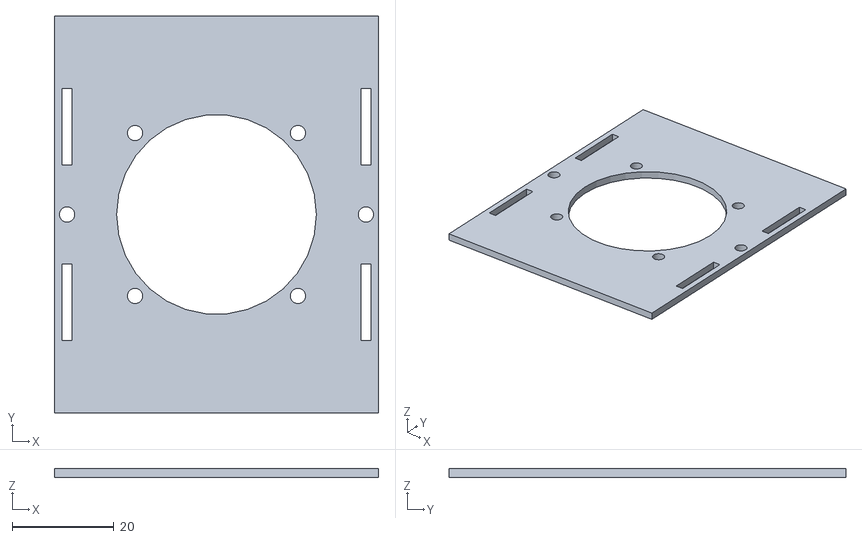
[picture p91: CAD file, 2014-09-08]
Hardware/yOPERO/CNC_shieldBox/STL/top.stl
63.7 x 78.0 x 1.80
