qvarker/Cyclone-PCB-Factory/Hardware/yOPERO/Cyclone_Template/output/template.dxf

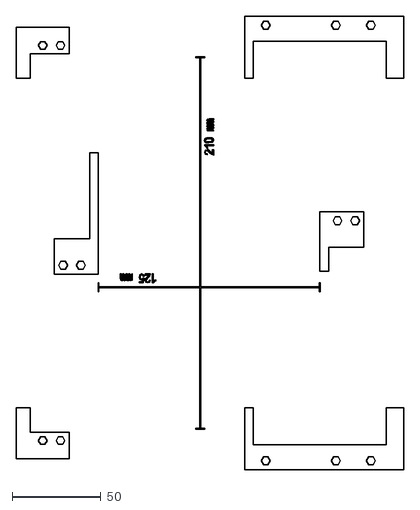
[picture p92: CAD file, 2014-09-08]
Hardware/yOPERO/Cyclone_Template/output/template.dxf
219.0 x 256.0
