qvarker/Cyclone-PCB-Factory/Hardware/yOPERO/Gears/stl/motor_gear.stl

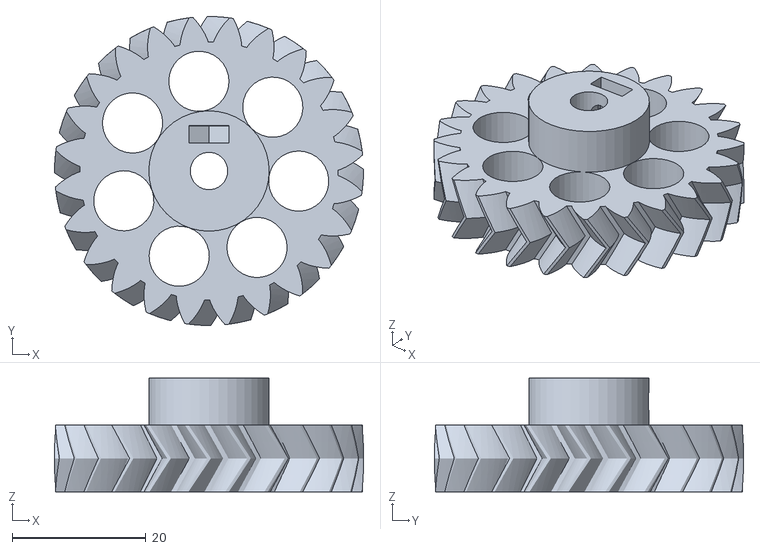
[picture p93: CAD file, 2014-09-08]
Hardware/yOPERO/Gears/stl/motor_gear.stl
46.2 x 46.2 x 17.0
