qvarker/Cyclone-PCB-Factory/Hardware/yOPERO/main_frame/stl/frame_hex_back support_no_motor.stl

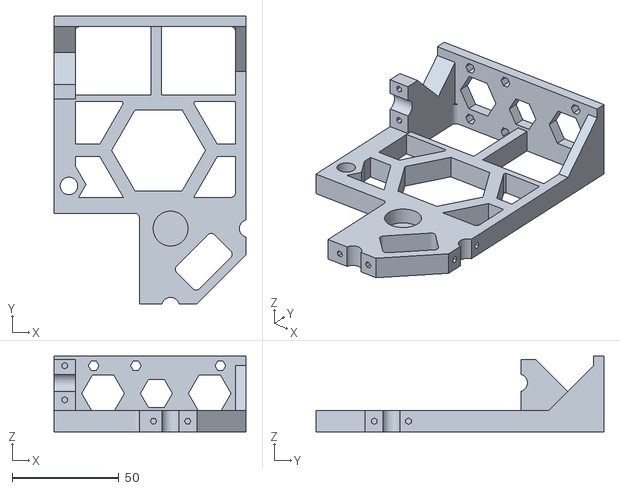
[picture p94: CAD file, 2014-09-08]
Hardware/yOPERO/main_frame/stl/frame_hex_back support_no_motor.stl
90.0 x 135.0 x 35.5
