qvarker/Cyclone-PCB-Factory/Hardware/yOPERO/smooth_rod_fix/stl/smooth_rod_fix_x4.stl

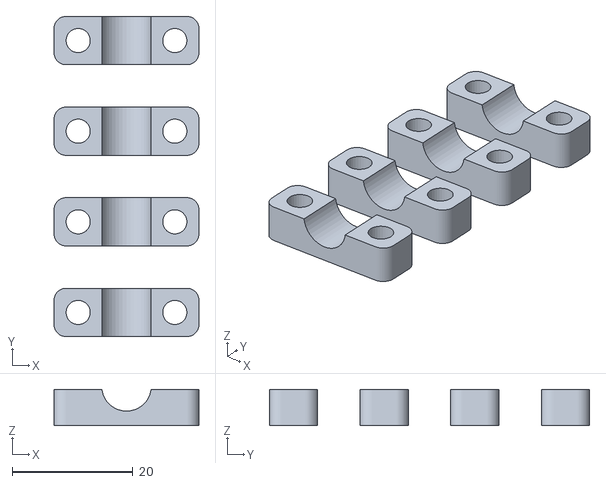
[picture p96: CAD file, 2014-09-08]
Hardware/yOPERO/smooth_rod_fix/stl/smooth_rod_fix_x4.stl
24.0 x 53.0 x 6.00
