qvarker/Cyclone-PCB-Factory/Hardware/yOPERO/XZ_axis/stl/not used/X_carriage.stl

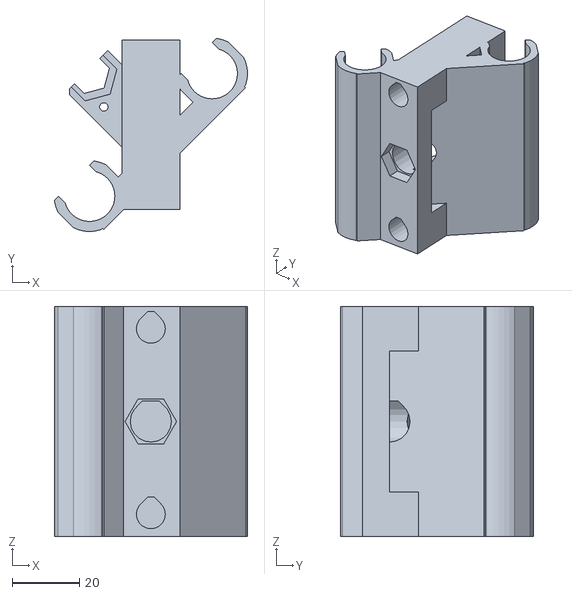
[picture p97: CAD file, 2014-09-08]
Hardware/yOPERO/XZ_axis/stl/not used/X_carriage.stl
57.3 x 57.3 x 68.2
