qvarker/Cyclone-PCB-Factory/Hardware/yOPERO/Y_axis/cycloneLogoC.dxf

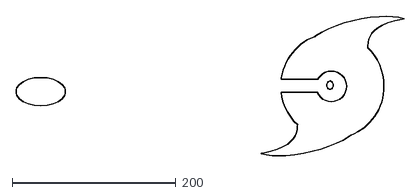
[picture p98: CAD file, 2014-09-08]
Hardware/yOPERO/Y_axis/cycloneLogoC.dxf
473.2 x 169.6
