qvarker/Cyclone-PCB-Factory/Hardware/CYCLONE_2/INHERITED/stl/Cyclone_Zcarriage.stl

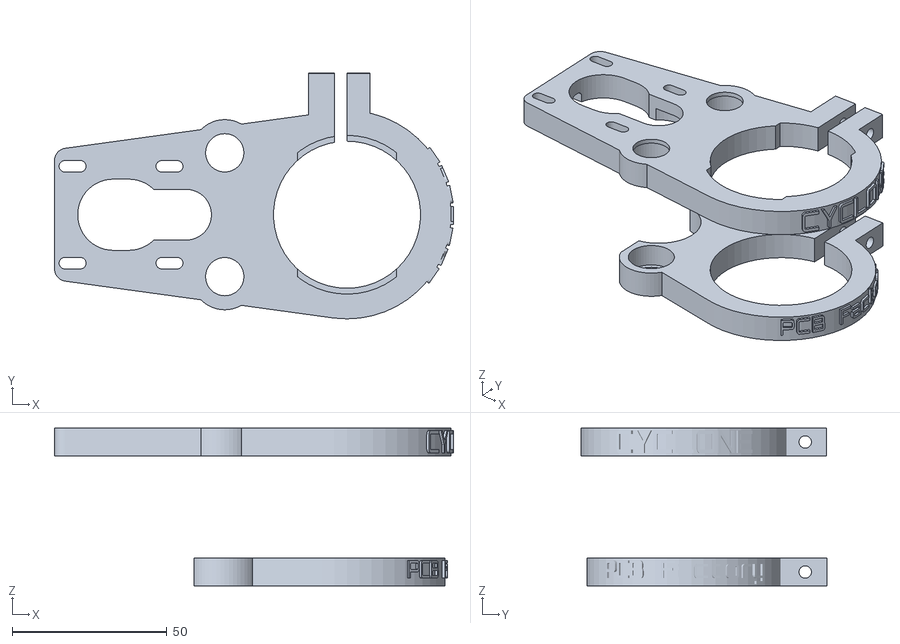
[picture p99: CAD file, 2014-09-08]
Hardware/CYCLONE_2/INHERITED/stl/Cyclone_Zcarriage.stl
128.9 x 79.4 x 51.0
