qvarker/Cyclone-PCB-Factory/Hardware/CYCLONE_2/output/Cyclone_YbackFrame.stl

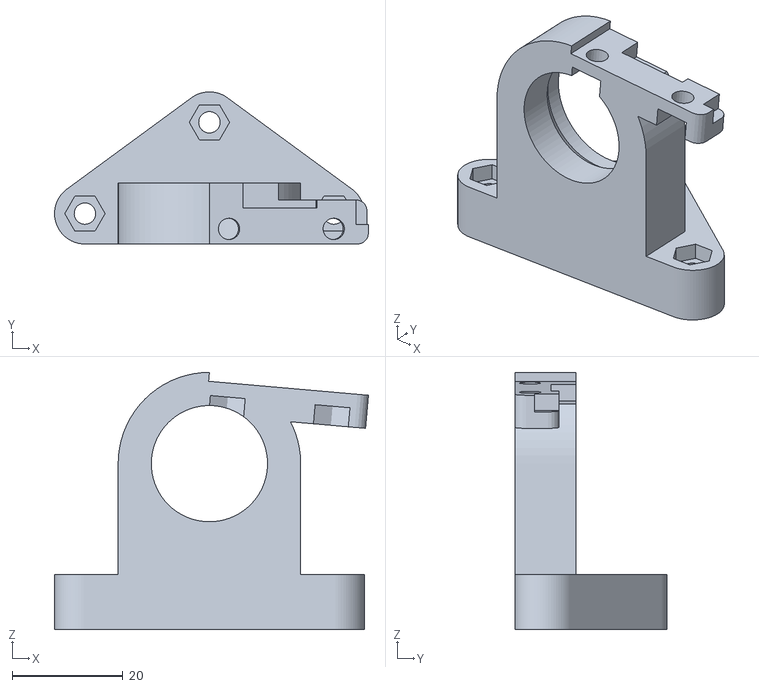
[picture p100: CAD file, 2014-09-08]
Hardware/CYCLONE_2/output/Cyclone_YbackFrame.stl
56.7 x 27.5 x 46.5
