qvarker/Cyclone-PCB-Factory/Hardware/CYCLONE_2/output/templates/laserCut/Cyclone_base_8mm.dxf

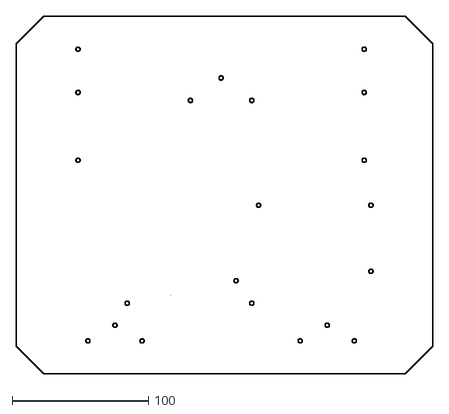
[picture p101: CAD file, 2014-08-22]
Hardware/CYCLONE_2/output/templates/laserCut/Cyclone_base_8mm.dxf
305.8 x 262.6
