qvarker/Cyclone-PCB-Factory/Hardware/CYCLONE_2/output/templates/laserCut/separate/Cyclone_workbed_drills.dxf

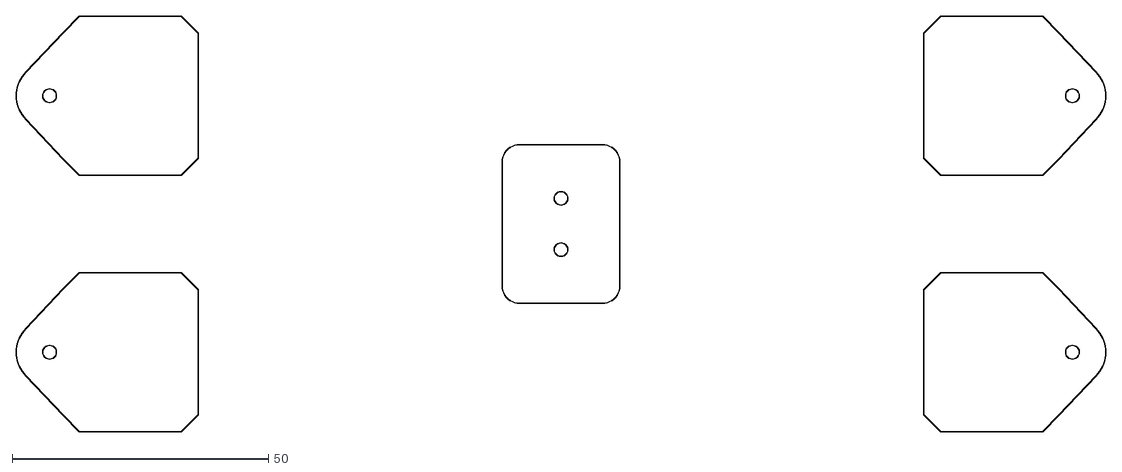
[picture p102: CAD file, 2014-08-22]
Hardware/CYCLONE_2/output/templates/laserCut/separate/Cyclone_workbed_drills.dxf
212.5 x 81.0
