qvarker/Cyclone-PCB-Factory/Hardware/Cyclone_Template/output/template_workbed_top.dxf

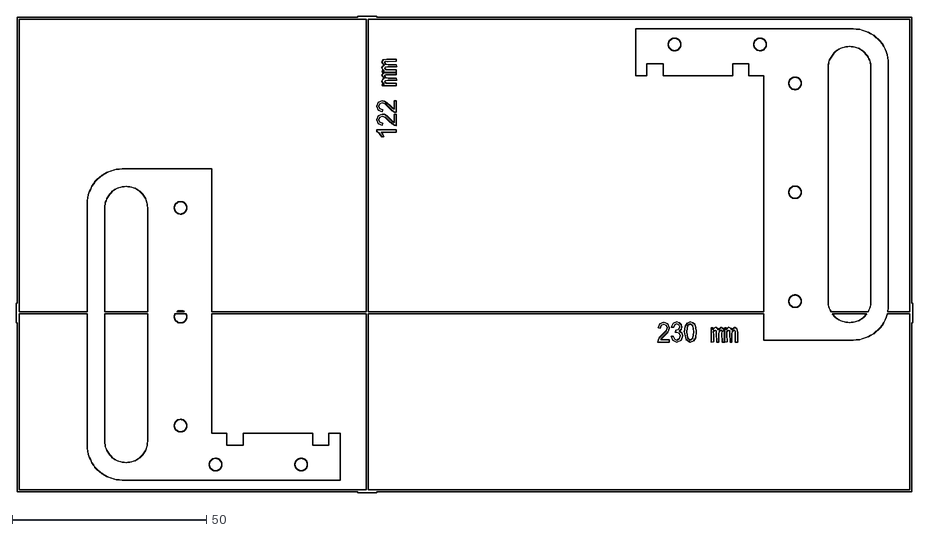
[picture p103: CAD file, 2014-09-08]
Hardware/Cyclone_Template/output/template_workbed_top.dxf
230.5 x 122.5
