qvarker/Cyclone-PCB-Factory/Hardware/smooth_rod_fix/stl/smooth_rod_fix_x8.stl

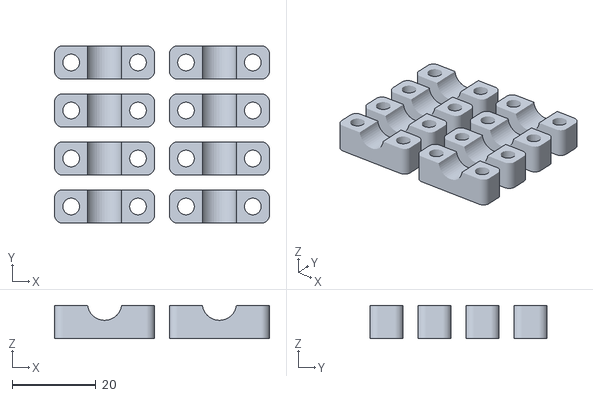
[picture p104: CAD file, 2014-09-08]
Hardware/smooth_rod_fix/stl/smooth_rod_fix_x8.stl
51.5 x 42.5 x 8.00
