qvarker/Cyclone-PCB-Factory/Hardware/XZ_axis/stl/Z_carriage_top.stl

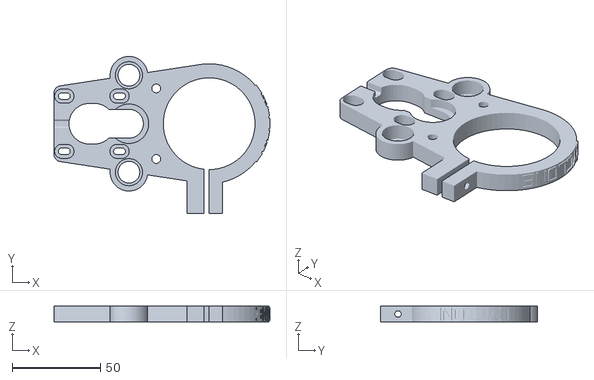
[picture p105: CAD file, 2014-09-08]
Hardware/XZ_axis/stl/Z_carriage_top.stl
122.5 x 89.2 x 9.00
