qvarker/Cyclone-PCB-Factory/Hardware/Y_axis/stl/linear_bearing_holder_x4.stl

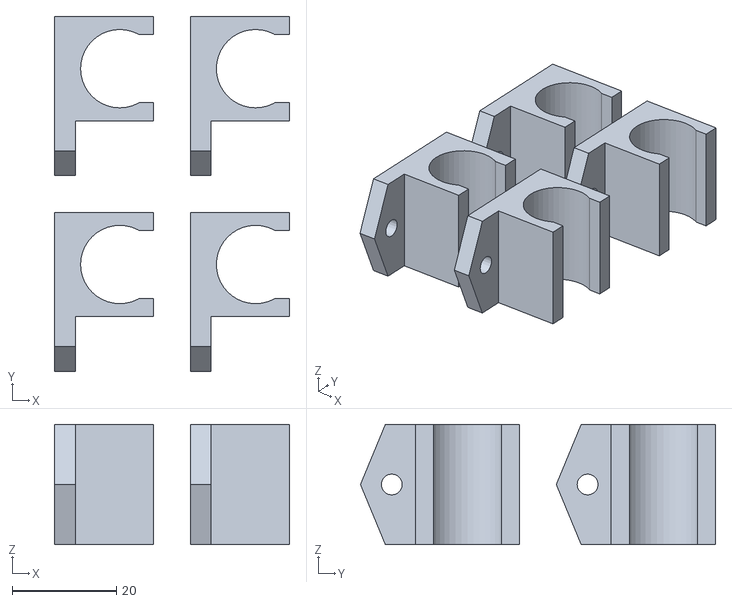
[picture p106: CAD file, 2014-09-08]
Hardware/Y_axis/stl/linear_bearing_holder_x4.stl
45.0 x 68.0 x 23.0
