qvarker/Cyclone-PCB-Factory/Hardware/yOPERO/smooth_rod_fix/stl/smooth_rod_fix.stl

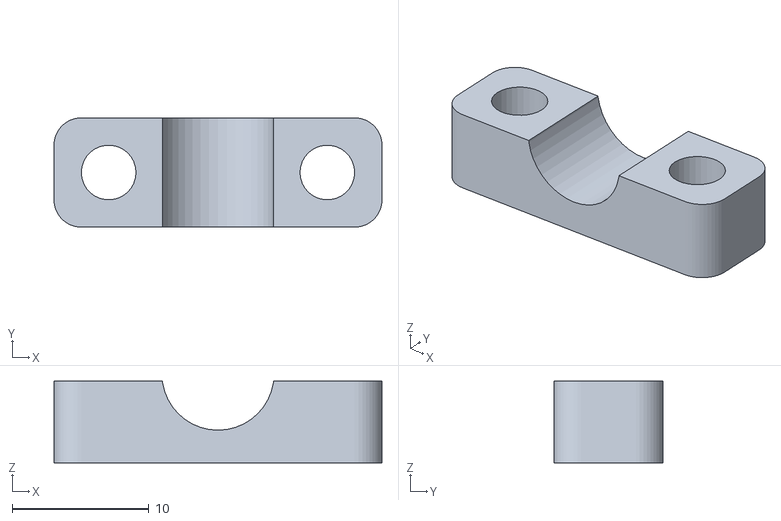
[picture p107: CAD file, 2014-09-08]
Hardware/yOPERO/smooth_rod_fix/stl/smooth_rod_fix.stl
24.0 x 8.00 x 6.00
