qvarker/Cyclone-PCB-Factory/Hardware/yOPERO/XZ_axis/stl/motor_gear.stl

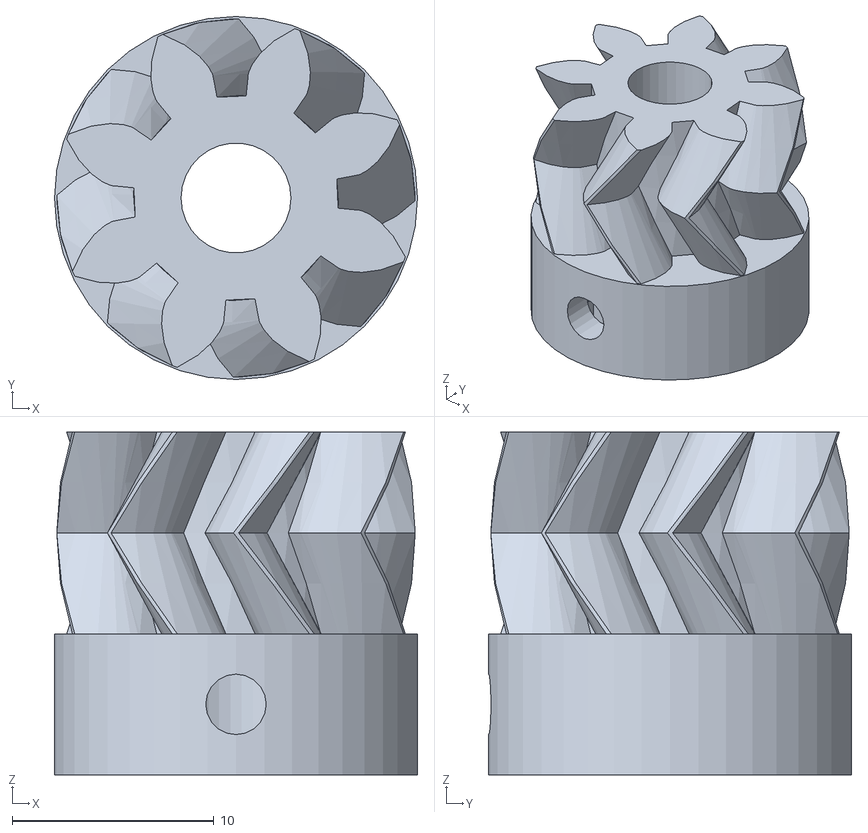
[picture p108: CAD file, 2014-09-08]
Hardware/yOPERO/XZ_axis/stl/motor_gear.stl
18.0 x 18.0 x 17.0
