qvarker/Cyclone-PCB-Factory/Hardware/yOPERO/XZ_axis/stl/not used/X_carriage_backlash_YOP.stl

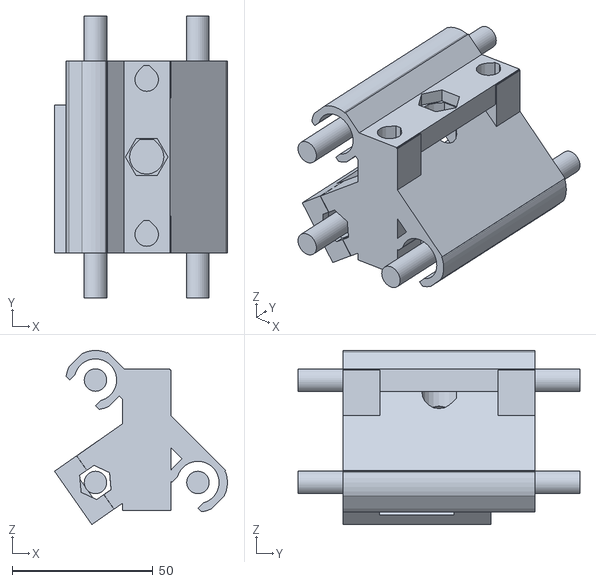
[picture p109: CAD file, 2014-09-08]
Hardware/yOPERO/XZ_axis/stl/not used/X_carriage_backlash_YOP.stl
61.4 x 100.0 x 61.8
