qvarker/Cyclone-PCB-Factory/Hardware/CYCLONE_2/freecad/Cyclone_X_carriage.fcstd

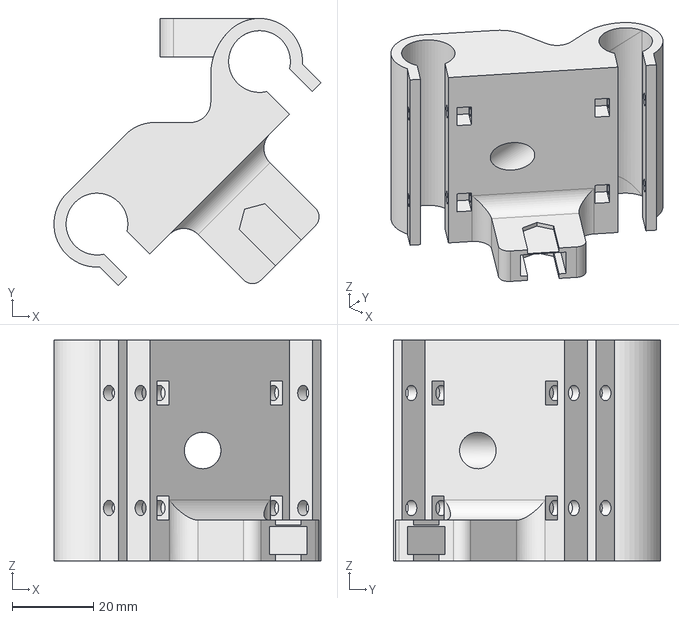
[picture p110: CAD file, 2014-09-08]
Hardware/CYCLONE_2/freecad/Cyclone_X_carriage.fcstd
65.7 x 65.7 x 54.3 mm
