qvarker/Cyclone-PCB-Factory/Hardware/CYCLONE_2/output/Cyclone_Ycarriage_linearBearingHolders.stl

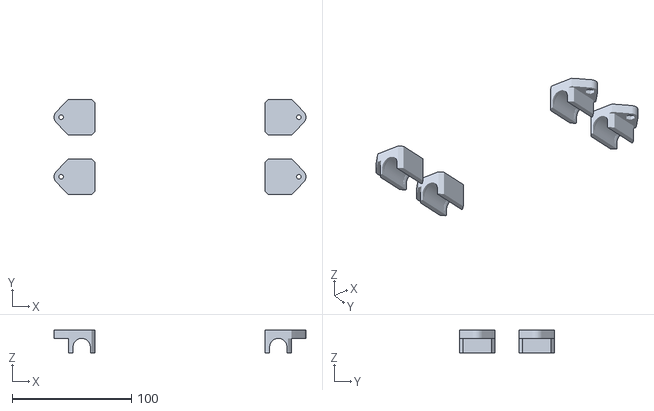
[picture p111: CAD file, 2014-09-08]
Hardware/CYCLONE_2/output/Cyclone_Ycarriage_linearBearingHolders.stl
211.5 x 80.0 x 19.2
