qvarker/Cyclone-PCB-Factory/Hardware/CYCLONE_2/output/templates/laserCut/separate/Cyclone_base_outline.dxf

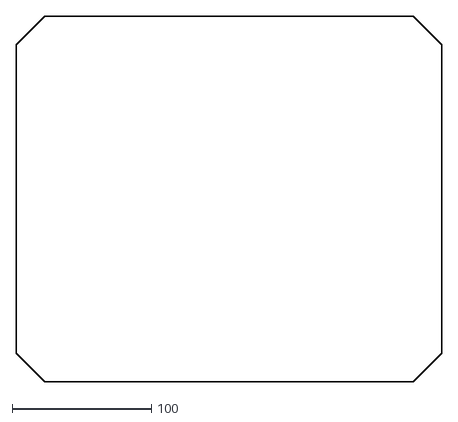
[picture p112: CAD file, 2014-08-22]
Hardware/CYCLONE_2/output/templates/laserCut/separate/Cyclone_base_outline.dxf
305.8 x 262.6
