qvarker/Cyclone-PCB-Factory/Hardware/Cyclone_Template/output/Cyclone.stl

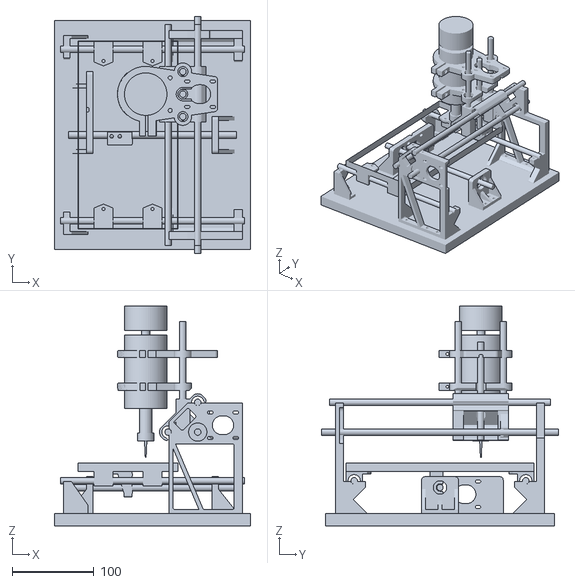
[picture p113: CAD file, 2014-09-08]
Hardware/Cyclone_Template/output/Cyclone.stl
240.0 x 290.0 x 268.8
