qvarker/Cyclone-PCB-Factory/Hardware/yOPERO/CNC_shieldBox/STL/right.stl

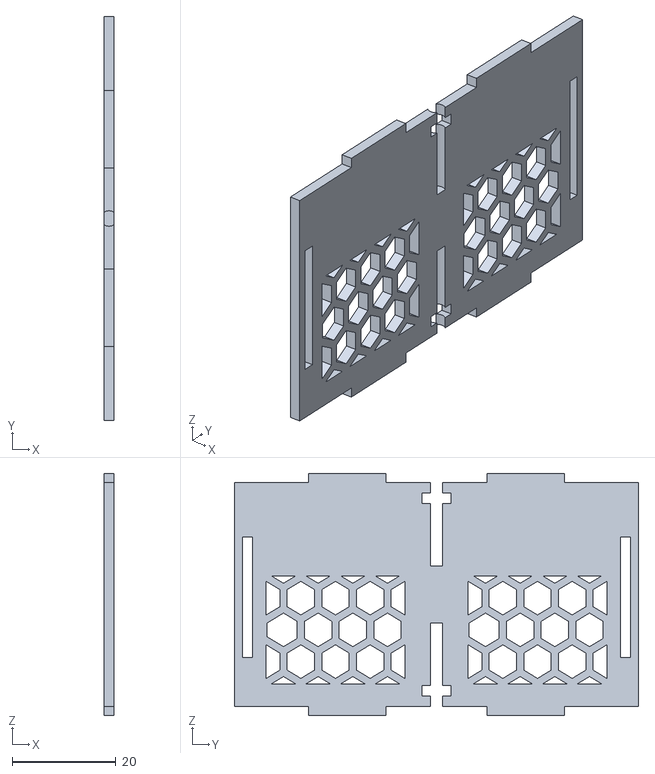
[picture p114: CAD file, 2014-09-08]
Hardware/yOPERO/CNC_shieldBox/STL/right.stl
2.00 x 78.0 x 46.8
