qvarker/Cyclone-PCB-Factory/Hardware/yOPERO/XZ_axis/stl/both_gears.stl

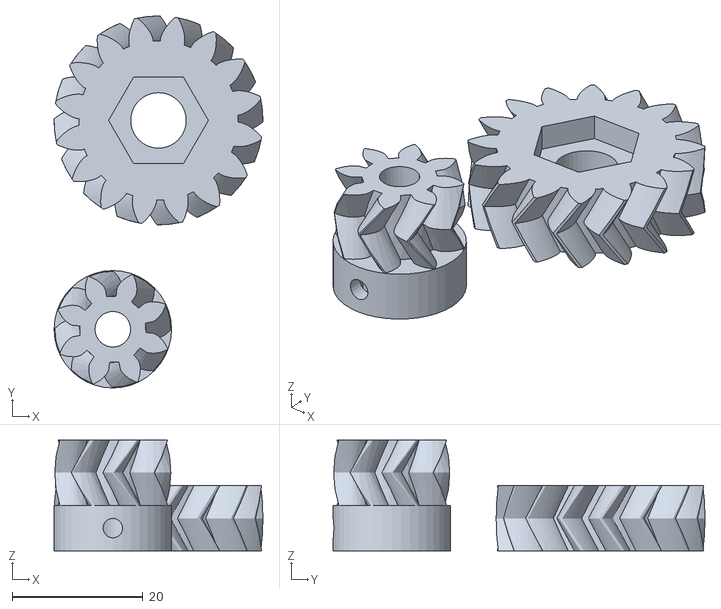
[picture p115: CAD file, 2014-09-08]
Hardware/yOPERO/XZ_axis/stl/both_gears.stl
32.0 x 57.0 x 17.0
