qvarker/Cyclone-PCB-Factory/Hardware/yOPERO/Y_axis/stl/not used/idle_stand.stl

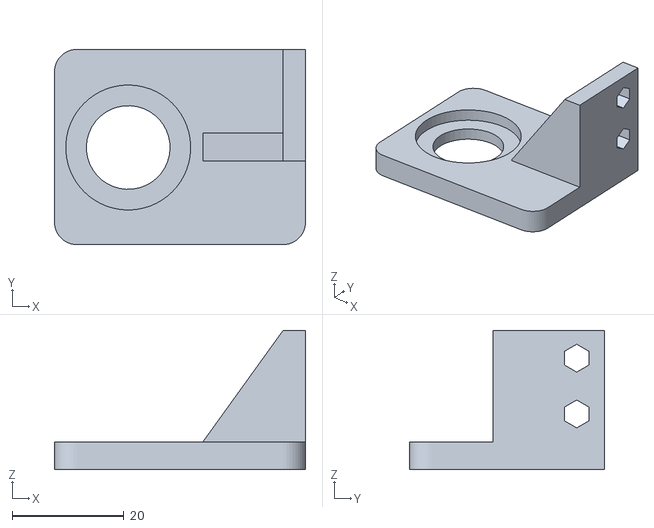
[picture p116: CAD file, 2014-09-08]
Hardware/yOPERO/Y_axis/stl/not used/idle_stand.stl
45.0 x 35.0 x 25.0
