qvarker/Cyclone-PCB-Factory/Hardware/CYCLONE_2/output/Cyclone_Ycarriage_nutHolder.stl

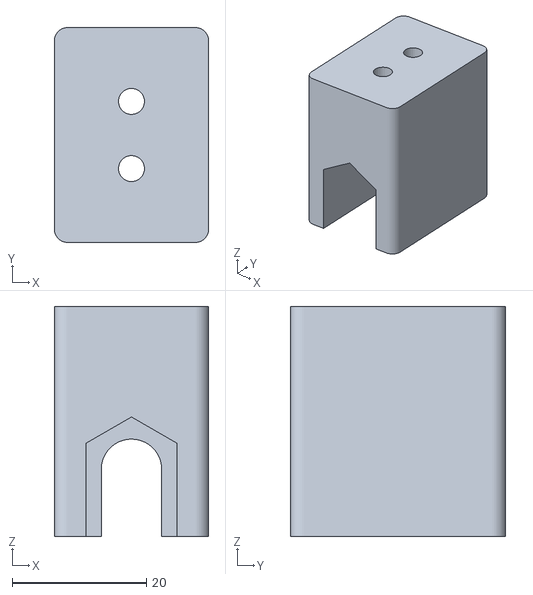
[picture p117: CAD file, 2014-09-08]
Hardware/CYCLONE_2/output/Cyclone_Ycarriage_nutHolder.stl
23.0 x 32.0 x 34.2
