qvarker/Cyclone-PCB-Factory/Hardware/yOPERO/Y_axis/stl/not used/motor_stand.stl

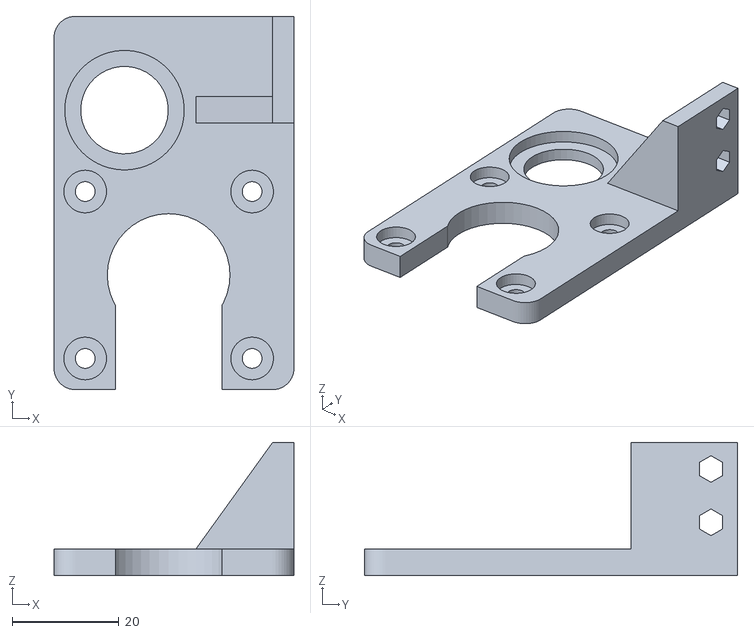
[picture p118: CAD file, 2014-09-08]
Hardware/yOPERO/Y_axis/stl/not used/motor_stand.stl
45.0 x 70.0 x 25.0
