qvarker/Cyclone-PCB-Factory/Hardware/yOPERO/Y_axis/stl/Y_rod_idler_YOP.stl

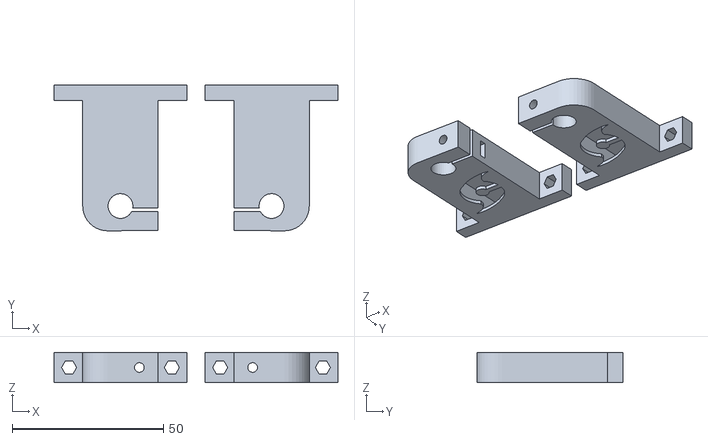
[picture p119: CAD file, 2014-09-08]
Hardware/yOPERO/Y_axis/stl/Y_rod_idler_YOP.stl
94.0 x 48.2 x 10.0
