qvarker/Cyclone-PCB-Factory/Hardware/CYCLONE_2/output/Cyclone_XrightFrame.stl

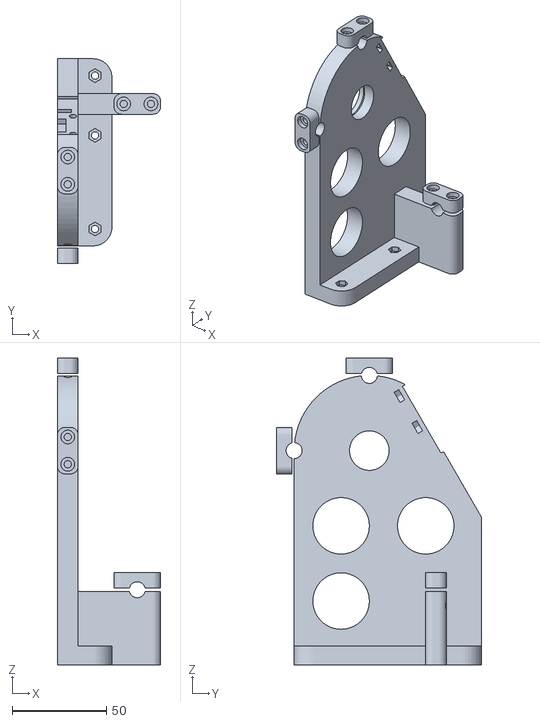
[picture p120: CAD file, 2014-09-08]
Hardware/CYCLONE_2/output/Cyclone_XrightFrame.stl
54.9 x 108.8 x 163.2
