qvarker/Cyclone-PCB-Factory/Hardware/yOPERO/XZ_axis/stl/Z_carriage.stl

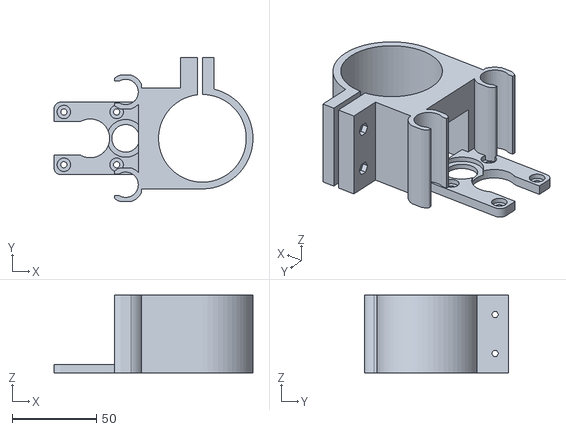
[picture p122: CAD file, 2014-09-08]
Hardware/yOPERO/XZ_axis/stl/Z_carriage.stl
118.0 x 85.5 x 46.0
