qvarker/Cyclone-PCB-Factory/Hardware/CYCLONE_2/output/Cyclone_Ycarriage_PCBholders.stl

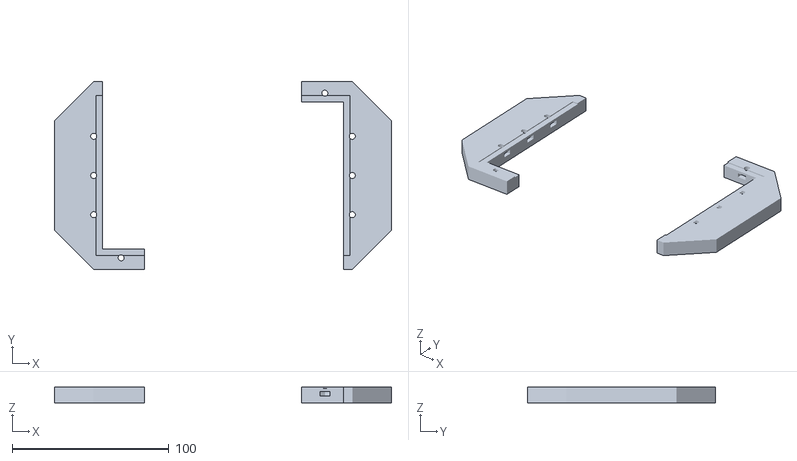
[picture p123: CAD file, 2014-09-08]
Hardware/CYCLONE_2/output/Cyclone_Ycarriage_PCBholders.stl
215.0 x 120.0 x 10.0
