qvarker/Cyclone-PCB-Factory/Hardware/CYCLONE_2/output/Cyclone_YfrontFrame.stl

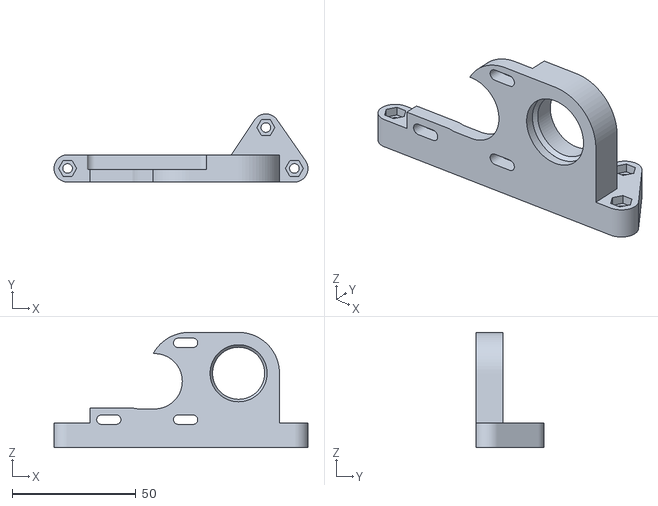
[picture p125: CAD file, 2014-09-08]
Hardware/CYCLONE_2/output/Cyclone_YfrontFrame.stl
102.5 x 27.5 x 46.5
