qvarker/Cyclone-PCB-Factory/Hardware/yOPERO/Y_axis/stl/linear_bearing_holder.stl

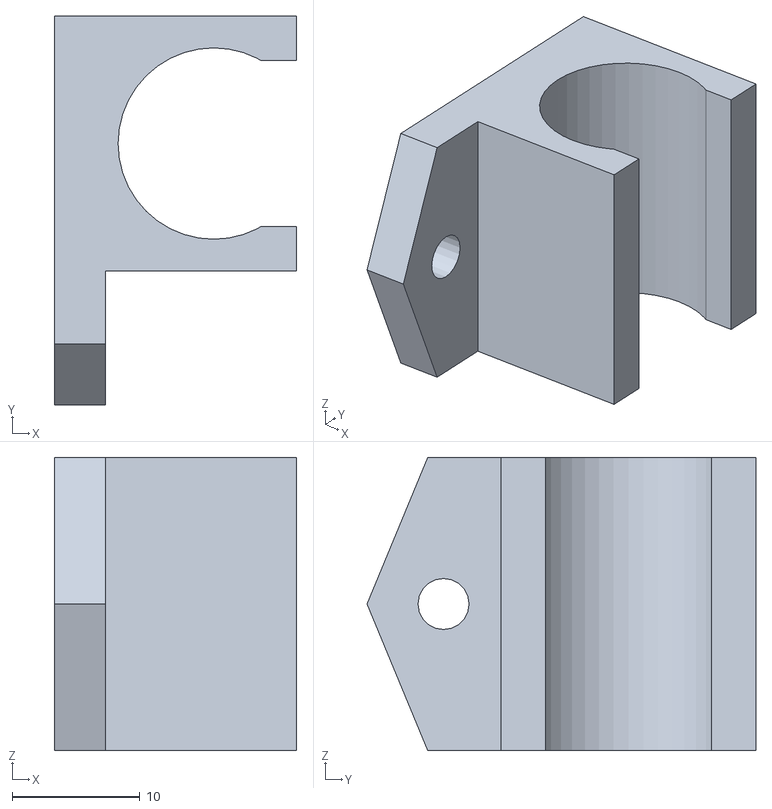
[picture p126: CAD file, 2014-09-08]
Hardware/yOPERO/Y_axis/stl/linear_bearing_holder.stl
19.0 x 30.5 x 23.0
