qvarker/Cyclone-PCB-Factory/Hardware/CYCLONE_2/output/Cyclone_XgearCover.stl

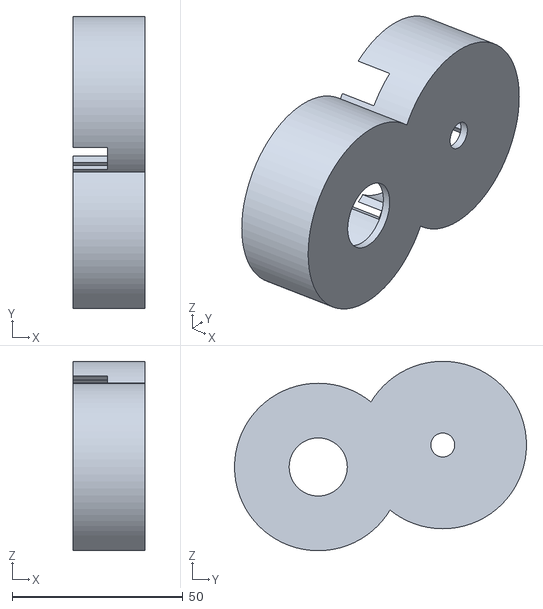
[picture p127: CAD file, 2014-08-22]
Hardware/CYCLONE_2/output/Cyclone_XgearCover.stl
21.0 x 85.4 x 55.4
