qvarker/Cyclone-PCB-Factory/Hardware/CYCLONE_2/output/Cyclone_Xcarriage.stl

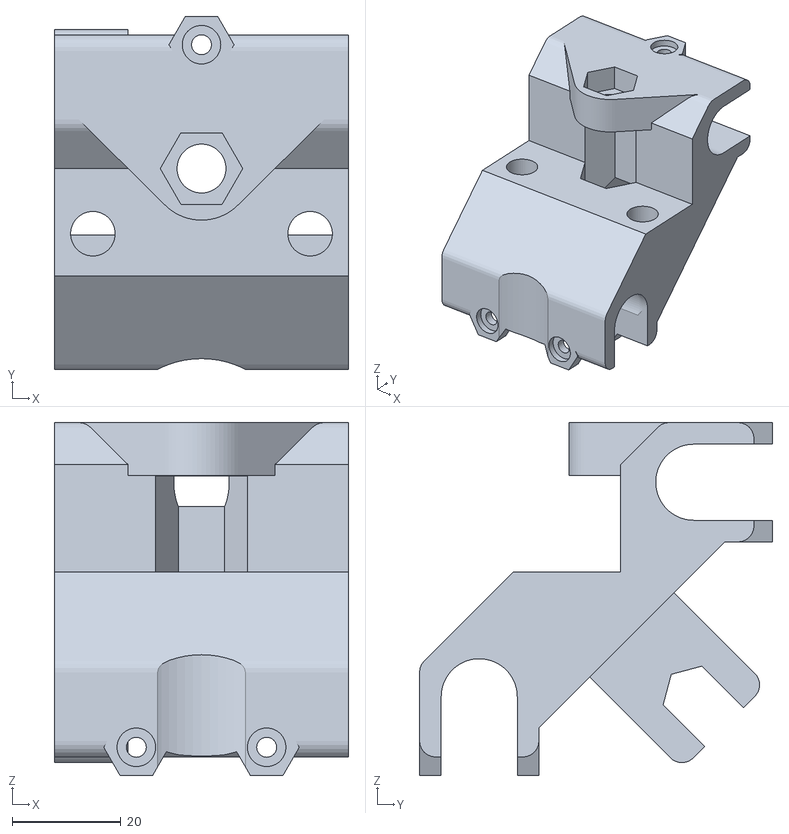
[picture p128: CAD file, 2014-08-22]
Hardware/CYCLONE_2/output/Cyclone_Xcarriage.stl
54.2 x 65.0 x 65.0
