qvarker/Cyclone-PCB-Factory/Hardware/yOPERO/CNC_shieldBox/Pictures/printed - Copy.gif

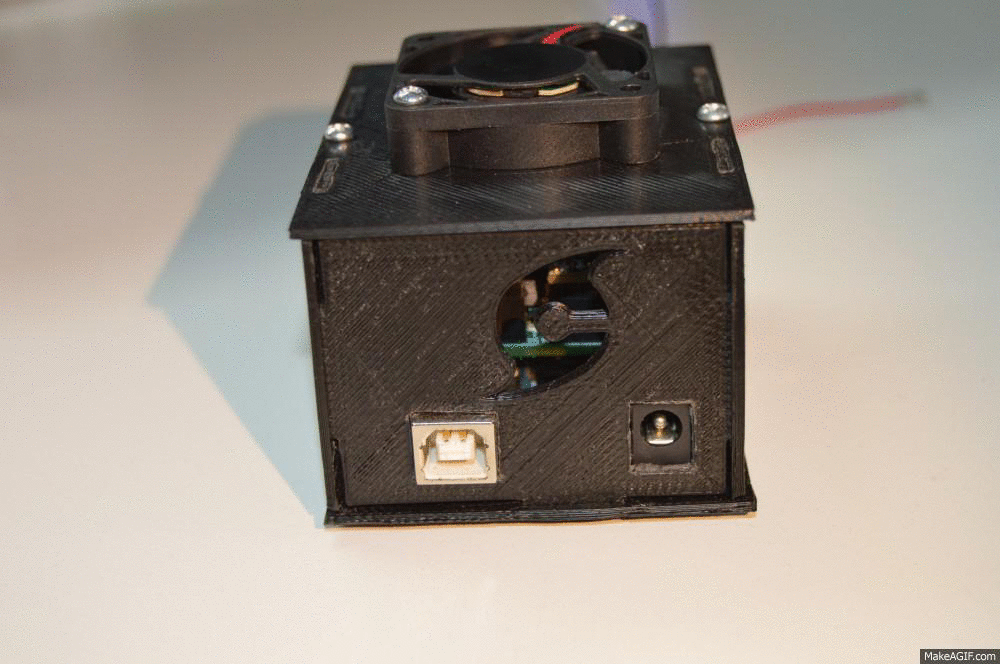
Hardware/yOPERO/CNC_shieldBox/Pictures/printed - Copy.gif
