qvarker/Cyclone-PCB-Factory/Software/PythonScripts/Images/Printshield.png

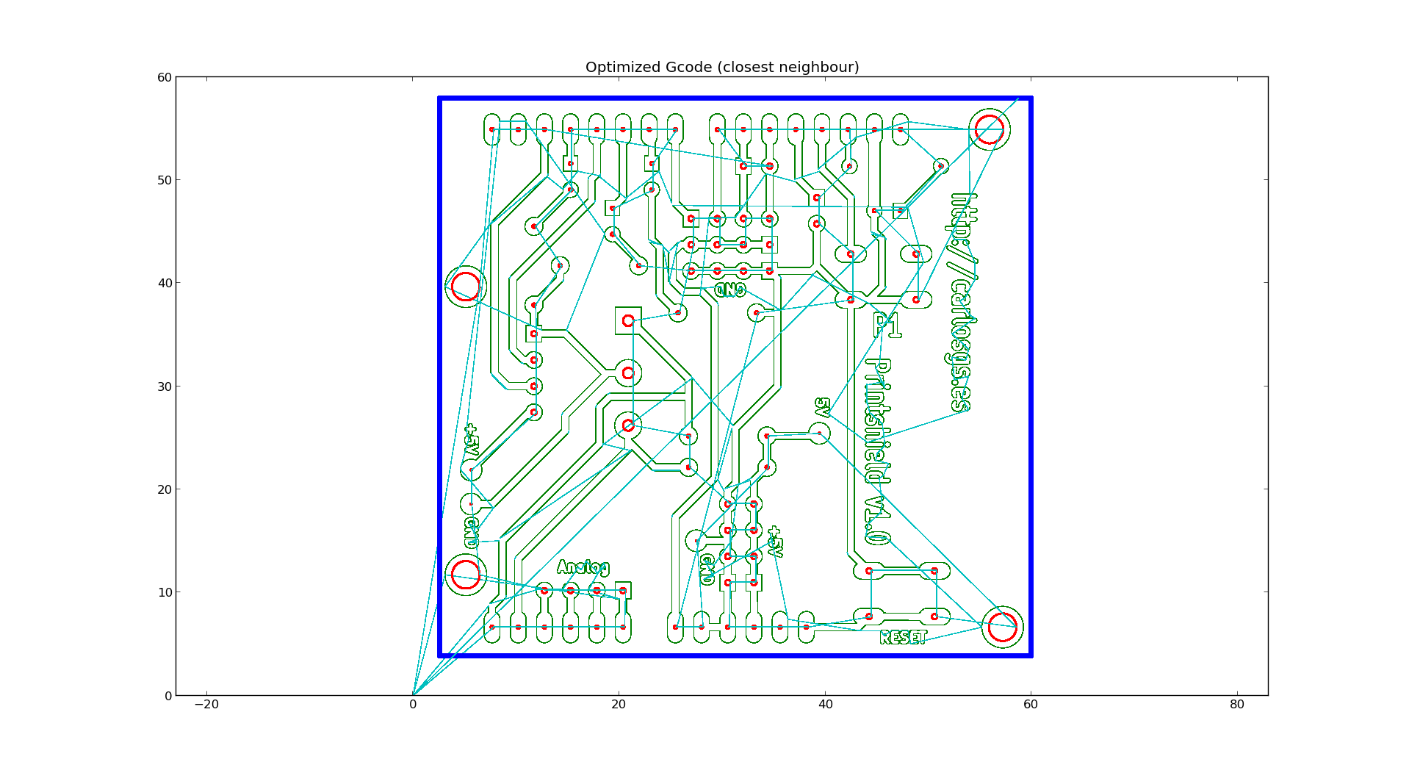
Software/PythonScripts/Images/Printshield.png
