qvarker/Cyclone-PCB-Factory/Software/PythonScripts/Images/Printshield_optimization.png

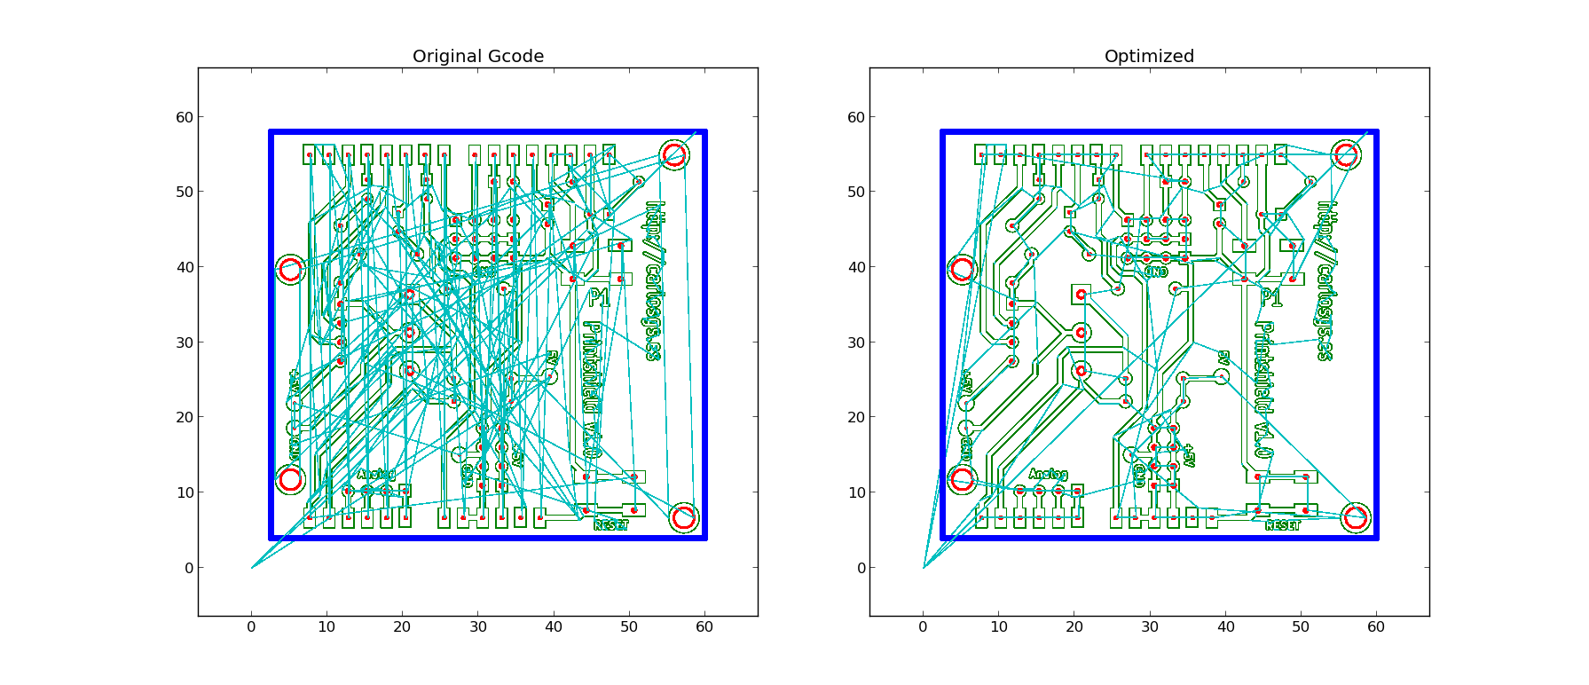
Software/PythonScripts/Images/Printshield_optimization.png
