qvarker/Cyclone-PCB-Factory/Software/PythonScripts/Images/Test_optimization.png

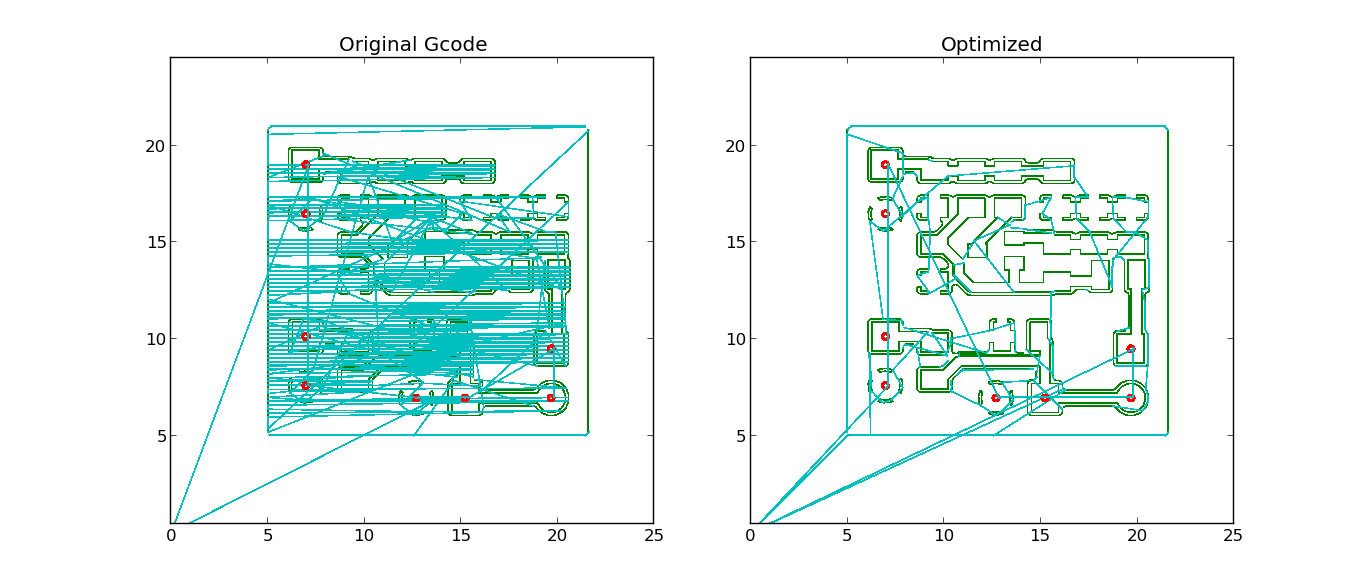
Software/PythonScripts/Images/Test_optimization.png
